HappyNapalm/HAD_CLOCK_191211/firmware/Capt_testboard_code/capt_testboard/usart_transfer_ring_buffer/source/usart_transfer_ring_buffer.c

/*
 * Copyright  2017 NXP
 * All rights reserved.
 *
 *
 * SPDX-License-Identifier: BSD-3-Clause
 */

#include "board.h"
#include "fsl_usart.h"

#include "pin_mux.h"
#include <stdbool.h>
/*******************************************************************************
 * Definitions
 ******************************************************************************/
#define EXAMPLE_USART USART0
#define EXAMPLE_USART_CLK_SRC kCLOCK_MainClk
#define EXAMPLE_USART_CLK_FREQ CLOCK_GetFreq(EXAMPLE_USART_CLK_SRC)
#define DELAY_TIME 0xFFFFFU

#define RX_RING_BUFFER_SIZE 20U
#define ECHO_BUFFER_SIZE 8U

/*******************************************************************************
 * Prototypes
 ******************************************************************************/
static void EXAMPLE_USARTUserCallback(USART_Type *base, usart_handle_t *handle, status_t status, void *userData);
static void EXAMPLE_USARTIinit(void);
static void EXAMPLE_USARTPrepareTransfer(void);

/*******************************************************************************
 * Variables
 ******************************************************************************/
usart_handle_t g_uartHandle;
uint8_t g_tipString[] = "USART RX ring buffer example.\r\nSend back received data.\r\nEcho every 8 bytes.\r\n";
uint8_t g_rxRingBuffer[RX_RING_BUFFER_SIZE] = {0}; /* RX ring buffer. */

uint8_t rxBuffer[ECHO_BUFFER_SIZE] = {0}; /* Buffer for receive data to echo. */
uint8_t txBuffer[ECHO_BUFFER_SIZE] = {0}; /* Buffer for send data to echo. */
volatile bool rxBufferEmpty        = true;
volatile bool txBufferFull         = false;
volatile bool txOnGoing            = false;
volatile bool rxOnGoing            = false;

usart_transfer_t xfer;
usart_transfer_t sendXfer;
usart_transfer_t receiveXfer;

/*******************************************************************************
 * Code
 ******************************************************************************/
/* USART user callback */
void EXAMPLE_USARTUserCallback(USART_Type *base, usart_handle_t *handle, status_t status, void *userData)
{
    userData = userData;

    if (kStatus_USART_TxIdle == status)
    {
        txBufferFull = false;
        txOnGoing    = false;
    }

    if (kStatus_USART_RxIdle == status)
    {
        rxBufferEmpty = false;
        rxOnGoing     = false;
    }
}

/*!
 * @brief Main function
 */
int main(void)
{
    size_t receivedBytes;

    /* Initialize the hardware. */
    /* Initialize the pins. */
    BOARD_InitPins();
    /* Enable clock. */
    BOARD_InitBootClocks();
    /* Select the main clock as source clock of USART0. */
    CLOCK_Select(kUART0_Clk_From_MainClk);

    /* Initialize the USART instance. */
    EXAMPLE_USARTIinit();

    /* Prepare for transactional transmission. */
    EXAMPLE_USARTPrepareTransfer();

    /* Send tip information. */
    txOnGoing = true;
    USART_TransferSendNonBlocking(EXAMPLE_USART, &g_uartHandle, &xfer);

    /* Wait transmit finished. */
    while (txOnGoing)
    {
    }

    while (1)
    {
        /* If txBuffer is empty and rxBuffer is full, copy rxBuffer to txBuffer. */
        if ((!rxBufferEmpty) && (!txBufferFull))
        {
            memcpy(txBuffer, rxBuffer, ECHO_BUFFER_SIZE);
            rxBufferEmpty = true;
            txBufferFull  = true;
        }

        /* If RX is idle and rxBuffer is empty, start to read data to rxBuffer. */
        if ((!rxOnGoing) && rxBufferEmpty)
        {
            rxOnGoing = true;
            USART_TransferReceiveNonBlocking(EXAMPLE_USART, &g_uartHandle, &receiveXfer, &receivedBytes);

            /* The receivedBytes is the current data size when API return, If this value equals to ECHO_BUFFER_SIZE,
             * it means all data were received from ring buffer.
             */
            if (ECHO_BUFFER_SIZE == receivedBytes)
            {
                rxBufferEmpty = false;
                rxOnGoing     = false;
            }
        }

        /* If TX is idle and txBuffer is full, start to send data. */
        if ((!txOnGoing) && txBufferFull)
        {
            txOnGoing = true;
            USART_TransferSendNonBlocking(EXAMPLE_USART, &g_uartHandle, &sendXfer);
        }
    }
}

static void EXAMPLE_USARTIinit(void)
{
    usart_config_t config;

    /* Default config by using USART_GetDefaultConfig():
     * config->baudRate_Bps = 9600U;
     * config->parityMode = kUSART_ParityDisabled;
     * config->stopBitCount = kUSART_OneStopBit;
     * config->bitCountPerChar = kUSART_8BitsPerChar;
     * config->loopback = false;
     * config->enableRx = false;
     * config->enableTx = false;
     * config->syncMode = kUSART_SyncModeDisabled;
     */
    USART_GetDefaultConfig(&config);
    config.baudRate_Bps = BOARD_DEBUG_USART_BAUDRATE;
    config.enableRx     = true;
    config.enableTx     = true;

    /* Initilize the USART with configuration. */
    USART_Init(EXAMPLE_USART, &config, EXAMPLE_USART_CLK_FREQ);
}
static void EXAMPLE_USARTPrepareTransfer(void)
{
    /* Create USART handle and install callback function. */
    USART_TransferCreateHandle(EXAMPLE_USART, &g_uartHandle, EXAMPLE_USARTUserCallback, NULL);
    /* Start ring buffer. */
    USART_TransferStartRingBuffer(EXAMPLE_USART, &g_uartHandle, g_rxRingBuffer, RX_RING_BUFFER_SIZE);

    /* Prepare transfer for sending tip string. */
    xfer.data     = g_tipString;
    xfer.dataSize = sizeof(g_tipString) - 1;

    /* Prepare transfer for sending the received characters. */
    sendXfer.data     = txBuffer;
    sendXfer.dataSize = ECHO_BUFFER_SIZE;

    /* Prepare transfer for receiving characters. */
    receiveXfer.data     = rxBuffer;
    receiveXfer.dataSize = ECHO_BUFFER_SIZE;
}
