HappyNapalm/HAD_CLOCK_191211/firmware/Capt_testboard_code/capt_testboard/gpio_led_output/source/gpio_led_output.c

/*
 * Copyright (c) 2015, Freescale Semiconductor, Inc.
 * Copyright 2016-2018 NXP
 * All rights reserved.
 *
 * SPDX-License-Identifier: BSD-3-Clause
 */

#include "board.h"
#include "fsl_debug_console.h"
#include "fsl_gpio.h"

#include "pin_mux.h"
/*******************************************************************************
 * Definitions
 ******************************************************************************/
#define APP_BOARD_TEST_LED_PORT 0U
#define APP_BOARD_TEST_LED_PIN 11U
#define APP_SW_PORT BOARD_SW1_GPIO_PORT
#define APP_SW_PIN BOARD_SW1_GPIO_PIN


/*******************************************************************************
 * Prototypes
 ******************************************************************************/
/*!
 * @brief delay a while.
 */
void delay(void);

/*******************************************************************************
 * Variables
 ******************************************************************************/

/*******************************************************************************
 * Code
 ******************************************************************************/
void delay(void)
{
    volatile uint32_t i = 0;
    for (i = 0; i < 100000; ++i)
    {
        __asm("NOP"); /* delay */
    }
}

/*!
 * @brief Main function
 */
int main(void)
{
    uint32_t port_state = 0;

    /* Define the init structure for the output LED pin*/
    gpio_pin_config_t led_config = {
        kGPIO_DigitalOutput,
        0,
    };

    /* Board pin, clock, debug console init */
    /* Select the main clock as source clock of USART0 (debug console) */
    CLOCK_Select(BOARD_DEBUG_USART_CLK_ATTACH);

    BOARD_InitPins();
    BOARD_InitBootClocks();
    BOARD_InitDebugConsole();

    /* Print a note to terminal. */
    PRINTF("\r\n GPIO Driver example\r\n");
    PRINTF("\r\n The LED is taking turns to shine.\r\n");

    /* Init output LED GPIO. */
    GPIO_PortInit(GPIO, APP_BOARD_TEST_LED_PORT);
    GPIO_PortInit(GPIO, APP_SW_PORT);
    GPIO_PinInit(GPIO, APP_BOARD_TEST_LED_PORT, APP_BOARD_TEST_LED_PIN, &led_config);
    GPIO_PinWrite(GPIO, APP_BOARD_TEST_LED_PORT, APP_BOARD_TEST_LED_PIN, 1);

    /* Port masking */
    GPIO_PortMaskedSet(GPIO, APP_BOARD_TEST_LED_PORT, 0x0000FFFF);
    GPIO_PortMaskedWrite(GPIO, APP_BOARD_TEST_LED_PORT, 0xFFFFFFFF);
    port_state = GPIO_PortRead(GPIO, APP_BOARD_TEST_LED_PORT);
    PRINTF("\r\n Standard port read: %x\r\n", port_state);
    port_state = GPIO_PortMaskedRead(GPIO, APP_BOARD_TEST_LED_PORT);
    PRINTF("\r\n Masked port read: %x\r\n", port_state);

    while (1)
    {
        port_state = GPIO_PortRead(GPIO, APP_SW_PORT);
        if (!(port_state & (1 << APP_SW_PIN)))
        {
            PRINTF("\r\n Port state: %x\r\n", port_state);
            GPIO_PortToggle(GPIO, APP_BOARD_TEST_LED_PORT, 1u << APP_BOARD_TEST_LED_PIN);
        }
        delay();
    }
}
