HappyNapalm/HAD_CLOCK_191211/firmware/Capt_testboard_code/capt_testboard/capt_acomp/device/LPC804.h

/*
** ###################################################################
**     Processors:          LPC804M101JDH20
**                          LPC804M101JDH24
**                          LPC804M101JHI33
**                          LPC804M111JDH24
**                          LPC804UK
**
**     Compilers:           GNU C Compiler
**                          IAR ANSI C/C++ Compiler for ARM
**                          Keil ARM C/C++ Compiler
**                          MCUXpresso Compiler
**
**     Reference manual:    LPC804 User manual Rev.1.0  24 Jan 2018
**     Version:             rev. 1.0, 2018-01-09
**     Build:               b190306
**
**     Abstract:
**         CMSIS Peripheral Access Layer for LPC804
**
**     Copyright 1997-2016 Freescale Semiconductor, Inc.
**     Copyright 2016-2019 NXP
**     All rights reserved.
**
**     SPDX-License-Identifier: BSD-3-Clause
**
**     http:                 www.nxp.com
**     mail:                 support@nxp.com
**
**     Revisions:
**     - rev. 1.0 (2018-01-09)
**         Initial version.
**
** ###################################################################
*/

/*!
 * @file LPC804.h
 * @version 1.0
 * @date 2018-01-09
 * @brief CMSIS Peripheral Access Layer for LPC804
 *
 * CMSIS Peripheral Access Layer for LPC804
 */

#ifndef _LPC804_H_
#define _LPC804_H_                               /**< Symbol preventing repeated inclusion */

/** Memory map major version (memory maps with equal major version number are
 * compatible) */
#define MCU_MEM_MAP_VERSION 0x0100U
/** Memory map minor version */
#define MCU_MEM_MAP_VERSION_MINOR 0x0000U


/* ----------------------------------------------------------------------------
   -- Interrupt vector numbers
   ---------------------------------------------------------------------------- */

/*!
 * @addtogroup Interrupt_vector_numbers Interrupt vector numbers
 * @{
 */

/** Interrupt Number Definitions */
#define NUMBER_OF_INT_VECTORS 48                 /**< Number of interrupts in the Vector table */

typedef enum IRQn {
  /* Auxiliary constants */
  NotAvail_IRQn                = -128,             /**< Not available device specific interrupt */

  /* Core interrupts */
  NonMaskableInt_IRQn          = -14,              /**< Non Maskable Interrupt */
  HardFault_IRQn               = -13,              /**< Cortex-M0 SV Hard Fault Interrupt */
  SVCall_IRQn                  = -5,               /**< Cortex-M0 SV Call Interrupt */
  PendSV_IRQn                  = -2,               /**< Cortex-M0 Pend SV Interrupt */
  SysTick_IRQn                 = -1,               /**< Cortex-M0 System Tick Interrupt */

  /* Device specific interrupts */
  SPI0_IRQn                    = 0,                /**< SPI0 interrupt */
  Reserved17_IRQn              = 1,                /**< Reserved interrupt */
  DAC0_IRQn                    = 2,                /**< DAC0 interrupt */
  USART0_IRQn                  = 3,                /**< USART0 interrupt */
  USART1_IRQn                  = 4,                /**< USART1 interrupt */
  Reserved21_IRQn              = 5,                /**< Reserved interrupt */
  Reserved22_IRQn              = 6,                /**< Reserved interrupt */
  I2C1_IRQn                    = 7,                /**< I2C1 interrupt */
  I2C0_IRQn                    = 8,                /**< I2C0 interrupt */
  Reserved25_IRQn              = 9,                /**< Reserved interrupt */
  MRT0_IRQn                    = 10,               /**< Multi-rate timer interrupt */
  CMP_CAPT_IRQn                = 11,               /**< Analog comparator interrupt or Capacitive Touch interrupt */
  WDT_IRQn                     = 12,               /**< Windowed watchdog timer interrupt */
  BOD_IRQn                     = 13,               /**< BOD interrupts */
  FLASH_IRQn                   = 14,               /**< flash interrupt */
  WKT_IRQn                     = 15,               /**< Self-wake-up timer interrupt */
  ADC_SEQA_IRQn                = 16,               /**< ADC sequence A completion. */
  ADC_SEQB_IRQn                = 17,               /**< ADC sequence B completion. */
  ADC_THCMP_IRQn               = 18,               /**< ADC threshold compare and error. */
  ADC_OVR_IRQn                 = 19,               /**< ADC overrun */
  Reserved36_IRQn              = 20,               /**< Reserved interrupt */
  Reserved37_IRQn              = 21,               /**< Reserved interrupt */
  Reserved38_IRQn              = 22,               /**< Reserved interrupt */
  CTIMER0_IRQn                 = 23,               /**< Timer interrupt */
  PIN_INT0_IRQn                = 24,               /**< Pin interrupt 0 or pattern match engine slice 0 interrupt */
  PIN_INT1_IRQn                = 25,               /**< Pin interrupt 1 or pattern match engine slice 1 interrupt */
  PIN_INT2_IRQn                = 26,               /**< Pin interrupt 2 or pattern match engine slice 2 interrupt */
  PIN_INT3_IRQn                = 27,               /**< Pin interrupt 3 or pattern match engine slice 3 interrupt */
  PIN_INT4_IRQn                = 28,               /**< Pin interrupt 4 or pattern match engine slice 4 interrupt */
  PIN_INT5_IRQn                = 29,               /**< Pin interrupt 5 or pattern match engine slice 5 interrupt */
  PIN_INT6_IRQn                = 30,               /**< Pin interrupt 6 or pattern match engine slice 6 interrupt */
  PIN_INT7_IRQn                = 31                /**< Pin interrupt 7 or pattern match engine slice 7 interrupt */
} IRQn_Type;

/*!
 * @}
 */ /* end of group Interrupt_vector_numbers */


/* ----------------------------------------------------------------------------
   -- Cortex M0 Core Configuration
   ---------------------------------------------------------------------------- */

/*!
 * @addtogroup Cortex_Core_Configuration Cortex M0 Core Configuration
 * @{
 */

#define __CM0PLUS_REV                  0x0000    /**< Core revision r0p0 */
#define __MPU_PRESENT                  0         /**< Defines if an MPU is present or not */
#define __VTOR_PRESENT                 1         /**< Defines if VTOR is present or not */
#define __NVIC_PRIO_BITS               2         /**< Number of priority bits implemented in the NVIC */
#define __Vendor_SysTickConfig         0         /**< Vendor specific implementation of SysTickConfig is defined */

#include "core_cm0plus.h"              /* Core Peripheral Access Layer */
#include "system_LPC804.h"             /* Device specific configuration file */

/*!
 * @}
 */ /* end of group Cortex_Core_Configuration */


/* ----------------------------------------------------------------------------
   -- Device Peripheral Access Layer
   ---------------------------------------------------------------------------- */

/*!
 * @addtogroup Peripheral_access_layer Device Peripheral Access Layer
 * @{
 */


/*
** Start of section using anonymous unions
*/

#if defined(__ARMCC_VERSION)
  #if (__ARMCC_VERSION >= 6010050)
    #pragma clang diagnostic push
  #else
    #pragma push
    #pragma anon_unions
  #endif
#elif defined(__GNUC__)
  /* anonymous unions are enabled by default */
#elif defined(__IAR_SYSTEMS_ICC__)
  #pragma language=extended
#else
  #error Not supported compiler type
#endif

/* ----------------------------------------------------------------------------
   -- ACOMP Peripheral Access Layer
   ---------------------------------------------------------------------------- */

/*!
 * @addtogroup ACOMP_Peripheral_Access_Layer ACOMP Peripheral Access Layer
 * @{
 */

/** ACOMP - Register Layout Typedef */
typedef struct {
  __IO uint32_t CTRL;                              /**< Comparator control register, offset: 0x0 */
  __IO uint32_t LAD;                               /**< Voltage ladder register, offset: 0x4 */
} ACOMP_Type;

/* ----------------------------------------------------------------------------
   -- ACOMP Register Masks
   ---------------------------------------------------------------------------- */

/*!
 * @addtogroup ACOMP_Register_Masks ACOMP Register Masks
 * @{
 */

/*! @name CTRL - Comparator control register */
/*! @{ */
#define ACOMP_CTRL_EDGESEL_MASK                  (0x18U)
#define ACOMP_CTRL_EDGESEL_SHIFT                 (3U)
/*! EDGESEL - This field controls which edges on the comparator output set the COMPEDGE bit (bit 23 below):
 *  0b00..Falling edges
 *  0b01..Rising edges
 *  0b10..Both edges
 *  0b11..Both edges
 */
#define ACOMP_CTRL_EDGESEL(x)                    (((uint32_t)(((uint32_t)(x)) << ACOMP_CTRL_EDGESEL_SHIFT)) & ACOMP_CTRL_EDGESEL_MASK)
#define ACOMP_CTRL_COMPSA_MASK                   (0x40U)
#define ACOMP_CTRL_COMPSA_SHIFT                  (6U)
/*! COMPSA - Comparator output control
 *  0b0..Comparator output is used directly.
 *  0b1..Comparator output is synchronized to the bus clock for output to other modules.
 */
#define ACOMP_CTRL_COMPSA(x)                     (((uint32_t)(((uint32_t)(x)) << ACOMP_CTRL_COMPSA_SHIFT)) & ACOMP_CTRL_COMPSA_MASK)
#define ACOMP_CTRL_COMP_VP_SEL_MASK              (0x700U)
#define ACOMP_CTRL_COMP_VP_SEL_SHIFT             (8U)
/*! COMP_VP_SEL - Selects positive voltage input
 *  0b000..VOLTAGE_LADDER_OUTPUT
 *  0b001..ACMP_I1
 *  0b010..ACMP_I2
 *  0b011..ACMP_I3
 *  0b100..ACMP_I4
 *  0b101..ACMP_I5
 *  0b110..Band gap. Internal reference voltage.
 *  0b111..DAC0 output
 */
#define ACOMP_CTRL_COMP_VP_SEL(x)                (((uint32_t)(((uint32_t)(x)) << ACOMP_CTRL_COMP_VP_SEL_SHIFT)) & ACOMP_CTRL_COMP_VP_SEL_MASK)
#define ACOMP_CTRL_COMP_VM_SEL_MASK              (0x3800U)
#define ACOMP_CTRL_COMP_VM_SEL_SHIFT             (11U)
/*! COMP_VM_SEL - Selects negative voltage input
 *  0b000..VOLTAGE_LADDER_OUTPUT
 *  0b001..ACMP_I1
 *  0b010..ACMP_I2
 *  0b011..ACMP_I3
 *  0b100..ACMP_I4
 *  0b101..ACMP_I5
 *  0b110..Band gap. Internal reference voltage.
 *  0b111..DAC0 output
 */
#define ACOMP_CTRL_COMP_VM_SEL(x)                (((uint32_t)(((uint32_t)(x)) << ACOMP_CTRL_COMP_VM_SEL_SHIFT)) & ACOMP_CTRL_COMP_VM_SEL_MASK)
#define ACOMP_CTRL_EDGECLR_MASK                  (0x100000U)
#define ACOMP_CTRL_EDGECLR_SHIFT                 (20U)
#define ACOMP_CTRL_EDGECLR(x)                    (((uint32_t)(((uint32_t)(x)) << ACOMP_CTRL_EDGECLR_SHIFT)) & ACOMP_CTRL_EDGECLR_MASK)
#define ACOMP_CTRL_COMPSTAT_MASK                 (0x200000U)
#define ACOMP_CTRL_COMPSTAT_SHIFT                (21U)
#define ACOMP_CTRL_COMPSTAT(x)                   (((uint32_t)(((uint32_t)(x)) << ACOMP_CTRL_COMPSTAT_SHIFT)) & ACOMP_CTRL_COMPSTAT_MASK)
#define ACOMP_CTRL_COMPEDGE_MASK                 (0x800000U)
#define ACOMP_CTRL_COMPEDGE_SHIFT                (23U)
#define ACOMP_CTRL_COMPEDGE(x)                   (((uint32_t)(((uint32_t)(x)) << ACOMP_CTRL_COMPEDGE_SHIFT)) & ACOMP_CTRL_COMPEDGE_MASK)
#define ACOMP_CTRL_INTENA_MASK                   (0x1000000U)
#define ACOMP_CTRL_INTENA_SHIFT                  (24U)
#define ACOMP_CTRL_INTENA(x)                     (((uint32_t)(((uint32_t)(x)) << ACOMP_CTRL_INTENA_SHIFT)) & ACOMP_CTRL_INTENA_MASK)
#define ACOMP_CTRL_HYS_MASK                      (0x6000000U)
#define ACOMP_CTRL_HYS_SHIFT                     (25U)
/*! HYS - Controls the hysteresis of the comparator. When the comparator is outputting a certain
 *    state, this is the difference between the selected signals, in the opposite direction from the
 *    state being output, that will switch the output.
 *  0b00..None (the output will switch as the voltages cross)
 *  0b01..5 mv
 *  0b10..10 mv
 *  0b11..20 mv
 */
#define ACOMP_CTRL_HYS(x)                        (((uint32_t)(((uint32_t)(x)) << ACOMP_CTRL_HYS_SHIFT)) & ACOMP_CTRL_HYS_MASK)
/*! @} */

/*! @name LAD - Voltage ladder register */
/*! @{ */
#define ACOMP_LAD_LADEN_MASK                     (0x1U)
#define ACOMP_LAD_LADEN_SHIFT                    (0U)
#define ACOMP_LAD_LADEN(x)                       (((uint32_t)(((uint32_t)(x)) << ACOMP_LAD_LADEN_SHIFT)) & ACOMP_LAD_LADEN_MASK)
#define ACOMP_LAD_LADSEL_MASK                    (0x3EU)
#define ACOMP_LAD_LADSEL_SHIFT                   (1U)
#define ACOMP_LAD_LADSEL(x)                      (((uint32_t)(((uint32_t)(x)) << ACOMP_LAD_LADSEL_SHIFT)) & ACOMP_LAD_LADSEL_MASK)
#define ACOMP_LAD_LADREF_MASK                    (0x40U)
#define ACOMP_LAD_LADREF_SHIFT                   (6U)
/*! LADREF - Selects the reference voltage Vref for the voltage ladder.
 *  0b0..Supply pin VDD
 *  0b1..VDDCMP pin
 */
#define ACOMP_LAD_LADREF(x)                      (((uint32_t)(((uint32_t)(x)) << ACOMP_LAD_LADREF_SHIFT)) & ACOMP_LAD_LADREF_MASK)
/*! @} */


/*!
 * @}
 */ /* end of group ACOMP_Register_Masks */


/* ACOMP - Peripheral instance base addresses */
/** Peripheral ACOMP base address */
#define ACOMP_BASE                               (0x40024000u)
/** Peripheral ACOMP base pointer */
#define ACOMP                                    ((ACOMP_Type *)ACOMP_BASE)
/** Array initializer of ACOMP peripheral base addresses */
#define ACOMP_BASE_ADDRS                         { ACOMP_BASE }
/** Array initializer of ACOMP peripheral base pointers */
#define ACOMP_BASE_PTRS                          { ACOMP }

/*!
 * @}
 */ /* end of group ACOMP_Peripheral_Access_Layer */


/* ----------------------------------------------------------------------------
   -- ADC Peripheral Access Layer
   ---------------------------------------------------------------------------- */

/*!
 * @addtogroup ADC_Peripheral_Access_Layer ADC Peripheral Access Layer
 * @{
 */

/** ADC - Register Layout Typedef */
typedef struct {
  __IO uint32_t CTRL;                              /**< ADC Control register. Contains the clock divide value, resolution selection, sampling time selection, and mode controls., offset: 0x0 */
       uint8_t RESERVED_0[4];
  __IO uint32_t SEQ_CTRL[2];                       /**< ADC Conversion Sequence-n control register: Controls triggering and channel selection for conversion sequence-n. Also specifies interrupt mode for sequence-n., array offset: 0x8, array step: 0x4 */
  __I  uint32_t SEQ_GDAT[2];                       /**< ADC Sequence-n Global Data register. This register contains the result of the most recent ADC conversion performed under sequence-n., array offset: 0x10, array step: 0x4 */
       uint8_t RESERVED_1[8];
  __I  uint32_t DAT[12];                           /**< ADC Channel N Data register. This register contains the result of the most recent conversion completed on channel N., array offset: 0x20, array step: 0x4 */
  __IO uint32_t THR0_LOW;                          /**< ADC Low Compare Threshold register 0: Contains the lower threshold level for automatic threshold comparison for any channels linked to threshold pair 0., offset: 0x50 */
  __IO uint32_t THR1_LOW;                          /**< ADC Low Compare Threshold register 1: Contains the lower threshold level for automatic threshold comparison for any channels linked to threshold pair 1., offset: 0x54 */
  __IO uint32_t THR0_HIGH;                         /**< ADC High Compare Threshold register 0: Contains the upper threshold level for automatic threshold comparison for any channels linked to threshold pair 0., offset: 0x58 */
  __IO uint32_t THR1_HIGH;                         /**< ADC High Compare Threshold register 1: Contains the upper threshold level for automatic threshold comparison for any channels linked to threshold pair 1., offset: 0x5C */
  __IO uint32_t CHAN_THRSEL;                       /**< ADC Channel-Threshold Select register. Specifies which set of threshold compare registers are to be used for each channel, offset: 0x60 */
  __IO uint32_t INTEN;                             /**< ADC Interrupt Enable register. This register contains enable bits that enable the sequence-A, sequence-B, threshold compare and data overrun interrupts to be generated., offset: 0x64 */
  __IO uint32_t FLAGS;                             /**< ADC Flags register. Contains the four interrupt/DMA trigger flags and the individual component overrun and threshold-compare flags. (The overrun bits replicate information stored in the result registers)., offset: 0x68 */
} ADC_Type;

/* ----------------------------------------------------------------------------
   -- ADC Register Masks
   ---------------------------------------------------------------------------- */

/*!
 * @addtogroup ADC_Register_Masks ADC Register Masks
 * @{
 */

/*! @name CTRL - ADC Control register. Contains the clock divide value, resolution selection, sampling time selection, and mode controls. */
/*! @{ */
#define ADC_CTRL_CLKDIV_MASK                     (0xFFU)
#define ADC_CTRL_CLKDIV_SHIFT                    (0U)
#define ADC_CTRL_CLKDIV(x)                       (((uint32_t)(((uint32_t)(x)) << ADC_CTRL_CLKDIV_SHIFT)) & ADC_CTRL_CLKDIV_MASK)
#define ADC_CTRL_LPWRMODE_MASK                   (0x400U)
#define ADC_CTRL_LPWRMODE_SHIFT                  (10U)
/*! LPWRMODE - The low-power ADC mode
 *  0b0..The low-power ADC mode is disabled. The analog circuitry remains activated even when no conversions are requested.
 *  0b1..The low-power ADC mode is enabled. The analog circuitry is automatically powered-down when no conversions
 *       are taking place. When any (hardware or software) triggering event is detected, the analog circuitry is
 *       enabled. After the required start-up time, the requested conversion will be launched. Once the conversion
 *       completes, the analog-circuitry will again be powered-down provided no further conversions are pending.
 *       Using this mode can save an appreciable amount of current (approximately 2.5 mA) when conversions are
 *       required relatively infrequently. The penalty for using this mode is an approximately FIFTEEN ADC CLOCK delay (30
 *       clocks in 10-bit mode), based on the frequency specified in the CLKDIV field, from the time the trigger
 *       event occurs until sampling of the A/D input commences. Note: This mode will NOT power-up the A/D if the
 *       ADC_ENA bit is low.
 */
#define ADC_CTRL_LPWRMODE(x)                     (((uint32_t)(((uint32_t)(x)) << ADC_CTRL_LPWRMODE_SHIFT)) & ADC_CTRL_LPWRMODE_MASK)
/*! @} */

/*! @name SEQ_CTRL - ADC Conversion Sequence-n control register: Controls triggering and channel selection for conversion sequence-n. Also specifies interrupt mode for sequence-n. */
/*! @{ */
#define ADC_SEQ_CTRL_CHANNELS_MASK               (0xFFFU)
#define ADC_SEQ_CTRL_CHANNELS_SHIFT              (0U)
#define ADC_SEQ_CTRL_CHANNELS(x)                 (((uint32_t)(((uint32_t)(x)) << ADC_SEQ_CTRL_CHANNELS_SHIFT)) & ADC_SEQ_CTRL_CHANNELS_MASK)
#define ADC_SEQ_CTRL_TRIGGER_MASK                (0x7000U)
#define ADC_SEQ_CTRL_TRIGGER_SHIFT               (12U)
#define ADC_SEQ_CTRL_TRIGGER(x)                  (((uint32_t)(((uint32_t)(x)) << ADC_SEQ_CTRL_TRIGGER_SHIFT)) & ADC_SEQ_CTRL_TRIGGER_MASK)
#define ADC_SEQ_CTRL_TRIGPOL_MASK                (0x40000U)
#define ADC_SEQ_CTRL_TRIGPOL_SHIFT               (18U)
/*! TRIGPOL - Select the polarity of the selected input trigger for this conversion sequence. In
 *    order to avoid generating a spurious trigger, it is recommended writing to this field only when
 *    SEQA_ENA (bit 31) is low. It is safe to change this field and set bit 31 in the same write.
 *  0b0..Negative edge. A negative edge launches the conversion sequence on the selected trigger input.
 *  0b1..Positive edge. A positive edge launches the conversion sequence on the selected trigger input.
 */
#define ADC_SEQ_CTRL_TRIGPOL(x)                  (((uint32_t)(((uint32_t)(x)) << ADC_SEQ_CTRL_TRIGPOL_SHIFT)) & ADC_SEQ_CTRL_TRIGPOL_MASK)
#define ADC_SEQ_CTRL_SYNCBYPASS_MASK             (0x80000U)
#define ADC_SEQ_CTRL_SYNCBYPASS_SHIFT            (19U)
/*! SYNCBYPASS - Setting this bit allows the hardware trigger input to bypass synchronization
 *    flip-flop stages and therefore shorten the time between the trigger input signal and the start of a
 *    conversion. There are slightly different criteria for whether or not this bit can be set
 *    depending on the clock operating mode: Synchronous mode (the ASYNMODE in the CTRL register = 0):
 *    Synchronization may be bypassed (this bit may be set) if the selected trigger source is already
 *    synchronous with the main system clock (eg. coming from an on-chip, system-clock-based timer).
 *    Whether this bit is set or not, a trigger pulse must be maintained for at least one system
 *    clock period. Asynchronous mode (the ASYNMODE in the CTRL register = 1): Synchronization may be
 *    bypassed (this bit may be set) if it is certain that the duration of a trigger input pulse
 *    will be at least one cycle of the ADC clock (regardless of whether the trigger comes from and
 *    on-chip or off-chip source). If this bit is NOT set, the trigger pulse must at least be
 *    maintained for one system clock period.
 *  0b0..Enable trigger synchronization. The hardware trigger bypass is not enabled.
 *  0b1..Bypass trigger synchronization. The hardware trigger bypass is enabled.
 */
#define ADC_SEQ_CTRL_SYNCBYPASS(x)               (((uint32_t)(((uint32_t)(x)) << ADC_SEQ_CTRL_SYNCBYPASS_SHIFT)) & ADC_SEQ_CTRL_SYNCBYPASS_MASK)
#define ADC_SEQ_CTRL_TSAMP_MASK                  (0x1F00000U)
#define ADC_SEQ_CTRL_TSAMP_SHIFT                 (20U)
#define ADC_SEQ_CTRL_TSAMP(x)                    (((uint32_t)(((uint32_t)(x)) << ADC_SEQ_CTRL_TSAMP_SHIFT)) & ADC_SEQ_CTRL_TSAMP_MASK)
#define ADC_SEQ_CTRL_START_MASK                  (0x4000000U)
#define ADC_SEQ_CTRL_START_SHIFT                 (26U)
#define ADC_SEQ_CTRL_START(x)                    (((uint32_t)(((uint32_t)(x)) << ADC_SEQ_CTRL_START_SHIFT)) & ADC_SEQ_CTRL_START_MASK)
#define ADC_SEQ_CTRL_BURST_MASK                  (0x8000000U)
#define ADC_SEQ_CTRL_BURST_SHIFT                 (27U)
#define ADC_SEQ_CTRL_BURST(x)                    (((uint32_t)(((uint32_t)(x)) << ADC_SEQ_CTRL_BURST_SHIFT)) & ADC_SEQ_CTRL_BURST_MASK)
#define ADC_SEQ_CTRL_SINGLESTEP_MASK             (0x10000000U)
#define ADC_SEQ_CTRL_SINGLESTEP_SHIFT            (28U)
#define ADC_SEQ_CTRL_SINGLESTEP(x)               (((uint32_t)(((uint32_t)(x)) << ADC_SEQ_CTRL_SINGLESTEP_SHIFT)) & ADC_SEQ_CTRL_SINGLESTEP_MASK)
#define ADC_SEQ_CTRL_LOWPRIO_MASK                (0x20000000U)
#define ADC_SEQ_CTRL_LOWPRIO_SHIFT               (29U)
/*! LOWPRIO - Set priority for sequence A.
 *  0b0..Low priority. Any B trigger which occurs while an A conversion sequence is active will be ignored and lost.
 *  0b1..High priority. Setting this bit to a 1 will permit any enabled B sequence trigger (including a B sequence
 *       software start) to immediately interrupt sequence A and launch a B sequence in it's place. The conversion
 *       currently in progress will be terminated. The A sequence that was interrupted will automatically resume
 *       after the B sequence completes. The channel whose conversion was terminated will be re-sampled and the
 *       conversion sequence will resume from that point.
 */
#define ADC_SEQ_CTRL_LOWPRIO(x)                  (((uint32_t)(((uint32_t)(x)) << ADC_SEQ_CTRL_LOWPRIO_SHIFT)) & ADC_SEQ_CTRL_LOWPRIO_MASK)
#define ADC_SEQ_CTRL_MODE_MASK                   (0x40000000U)
#define ADC_SEQ_CTRL_MODE_SHIFT                  (30U)
/*! MODE - Indicates whether the primary method for retrieving conversion results for this sequence
 *    will be accomplished via reading the global data register (SEQA_GDAT) at the end of each
 *    conversion, or the individual channel result registers at the end of the entire sequence. Impacts
 *    when conversion-complete interrupt/DMA trigger for sequence-A will be generated and which
 *    overrun conditions contribute to an overrun interrupt as described below.
 *  0b0..End of conversion. The sequence A interrupt/DMA trigger will be set at the end of each individual ADC
 *       conversion performed under sequence A. This flag will mirror the DATAVALID bit in the SEQA_GDAT register. The
 *       OVERRUN bit in the SEQA_GDAT register will contribute to generation of an overrun interrupt/DMA trigger
 *       if enabled.
 *  0b1..End of sequence. The sequence A interrupt/DMA trigger will be set when the entire set of sequence-A
 *       conversions completes. This flag will need to be explicitly cleared by software or by the DMA-clear signal in
 *       this mode. The OVERRUN bit in the SEQA_GDAT register will NOT contribute to generation of an overrun
 *       interrupt/DMA trigger since it is assumed this register may not be utilized in this mode.
 */
#define ADC_SEQ_CTRL_MODE(x)                     (((uint32_t)(((uint32_t)(x)) << ADC_SEQ_CTRL_MODE_SHIFT)) & ADC_SEQ_CTRL_MODE_MASK)
#define ADC_SEQ_CTRL_SEQ_ENA_MASK                (0x80000000U)
#define ADC_SEQ_CTRL_SEQ_ENA_SHIFT               (31U)
/*! SEQ_ENA - Sequence Enable. In order to avoid spuriously triggering the sequence, care should be
 *    taken to only set the SEQn_ENA bit when the selected trigger input is in its INACTIVE state
 *    (as defined by the TRIGPOL bit). If this condition is not met, the sequence will be triggered
 *    immediately upon being enabled. In order to avoid spuriously triggering the sequence, care
 *    should be taken to only set the SEQn_ENA bit when the selected trigger input is in its INACTIVE
 *    state (as defined by the TRIGPOL bit). If this condition is not met, the sequence will be
 *    triggered immediately upon being enabled.
 *  0b0..Disabled. Sequence n is disabled. Sequence n triggers are ignored. If this bit is cleared while sequence
 *       n is in progress, the sequence will be halted at the end of the current conversion. After the sequence is
 *       re-enabled, a new trigger will be required to restart the sequence beginning with the next enabled channel.
 *  0b1..Enabled. Sequence n is enabled.
 */
#define ADC_SEQ_CTRL_SEQ_ENA(x)                  (((uint32_t)(((uint32_t)(x)) << ADC_SEQ_CTRL_SEQ_ENA_SHIFT)) & ADC_SEQ_CTRL_SEQ_ENA_MASK)
/*! @} */

/* The count of ADC_SEQ_CTRL */
#define ADC_SEQ_CTRL_COUNT                       (2U)

/*! @name SEQ_GDAT - ADC Sequence-n Global Data register. This register contains the result of the most recent ADC conversion performed under sequence-n. */
/*! @{ */
#define ADC_SEQ_GDAT_RESULT_MASK                 (0xFFF0U)
#define ADC_SEQ_GDAT_RESULT_SHIFT                (4U)
#define ADC_SEQ_GDAT_RESULT(x)                   (((uint32_t)(((uint32_t)(x)) << ADC_SEQ_GDAT_RESULT_SHIFT)) & ADC_SEQ_GDAT_RESULT_MASK)
#define ADC_SEQ_GDAT_THCMPRANGE_MASK             (0x30000U)
#define ADC_SEQ_GDAT_THCMPRANGE_SHIFT            (16U)
#define ADC_SEQ_GDAT_THCMPRANGE(x)               (((uint32_t)(((uint32_t)(x)) << ADC_SEQ_GDAT_THCMPRANGE_SHIFT)) & ADC_SEQ_GDAT_THCMPRANGE_MASK)
#define ADC_SEQ_GDAT_THCMPCROSS_MASK             (0xC0000U)
#define ADC_SEQ_GDAT_THCMPCROSS_SHIFT            (18U)
#define ADC_SEQ_GDAT_THCMPCROSS(x)               (((uint32_t)(((uint32_t)(x)) << ADC_SEQ_GDAT_THCMPCROSS_SHIFT)) & ADC_SEQ_GDAT_THCMPCROSS_MASK)
#define ADC_SEQ_GDAT_CHN_MASK                    (0x3C000000U)
#define ADC_SEQ_GDAT_CHN_SHIFT                   (26U)
#define ADC_SEQ_GDAT_CHN(x)                      (((uint32_t)(((uint32_t)(x)) << ADC_SEQ_GDAT_CHN_SHIFT)) & ADC_SEQ_GDAT_CHN_MASK)
#define ADC_SEQ_GDAT_OVERRUN_MASK                (0x40000000U)
#define ADC_SEQ_GDAT_OVERRUN_SHIFT               (30U)
#define ADC_SEQ_GDAT_OVERRUN(x)                  (((uint32_t)(((uint32_t)(x)) << ADC_SEQ_GDAT_OVERRUN_SHIFT)) & ADC_SEQ_GDAT_OVERRUN_MASK)
#define ADC_SEQ_GDAT_DATAVALID_MASK              (0x80000000U)
#define ADC_SEQ_GDAT_DATAVALID_SHIFT             (31U)
#define ADC_SEQ_GDAT_DATAVALID(x)                (((uint32_t)(((uint32_t)(x)) << ADC_SEQ_GDAT_DATAVALID_SHIFT)) & ADC_SEQ_GDAT_DATAVALID_MASK)
/*! @} */

/* The count of ADC_SEQ_GDAT */
#define ADC_SEQ_GDAT_COUNT                       (2U)

/*! @name DAT - ADC Channel N Data register. This register contains the result of the most recent conversion completed on channel N. */
/*! @{ */
#define ADC_DAT_RESULT_MASK                      (0xFFF0U)
#define ADC_DAT_RESULT_SHIFT                     (4U)
#define ADC_DAT_RESULT(x)                        (((uint32_t)(((uint32_t)(x)) << ADC_DAT_RESULT_SHIFT)) & ADC_DAT_RESULT_MASK)
#define ADC_DAT_THCMPRANGE_MASK                  (0x30000U)
#define ADC_DAT_THCMPRANGE_SHIFT                 (16U)
#define ADC_DAT_THCMPRANGE(x)                    (((uint32_t)(((uint32_t)(x)) << ADC_DAT_THCMPRANGE_SHIFT)) & ADC_DAT_THCMPRANGE_MASK)
#define ADC_DAT_THCMPCROSS_MASK                  (0xC0000U)
#define ADC_DAT_THCMPCROSS_SHIFT                 (18U)
#define ADC_DAT_THCMPCROSS(x)                    (((uint32_t)(((uint32_t)(x)) << ADC_DAT_THCMPCROSS_SHIFT)) & ADC_DAT_THCMPCROSS_MASK)
#define ADC_DAT_CHANNEL_MASK                     (0x3C000000U)
#define ADC_DAT_CHANNEL_SHIFT                    (26U)
#define ADC_DAT_CHANNEL(x)                       (((uint32_t)(((uint32_t)(x)) << ADC_DAT_CHANNEL_SHIFT)) & ADC_DAT_CHANNEL_MASK)
#define ADC_DAT_OVERRUN_MASK                     (0x40000000U)
#define ADC_DAT_OVERRUN_SHIFT                    (30U)
#define ADC_DAT_OVERRUN(x)                       (((uint32_t)(((uint32_t)(x)) << ADC_DAT_OVERRUN_SHIFT)) & ADC_DAT_OVERRUN_MASK)
#define ADC_DAT_DATAVALID_MASK                   (0x80000000U)
#define ADC_DAT_DATAVALID_SHIFT                  (31U)
#define ADC_DAT_DATAVALID(x)                     (((uint32_t)(((uint32_t)(x)) << ADC_DAT_DATAVALID_SHIFT)) & ADC_DAT_DATAVALID_MASK)
/*! @} */

/* The count of ADC_DAT */
#define ADC_DAT_COUNT                            (12U)

/*! @name THR0_LOW - ADC Low Compare Threshold register 0: Contains the lower threshold level for automatic threshold comparison for any channels linked to threshold pair 0. */
/*! @{ */
#define ADC_THR0_LOW_THRLOW_MASK                 (0xFFF0U)
#define ADC_THR0_LOW_THRLOW_SHIFT                (4U)
#define ADC_THR0_LOW_THRLOW(x)                   (((uint32_t)(((uint32_t)(x)) << ADC_THR0_LOW_THRLOW_SHIFT)) & ADC_THR0_LOW_THRLOW_MASK)
/*! @} */

/*! @name THR1_LOW - ADC Low Compare Threshold register 1: Contains the lower threshold level for automatic threshold comparison for any channels linked to threshold pair 1. */
/*! @{ */
#define ADC_THR1_LOW_THRLOW_MASK                 (0xFFF0U)
#define ADC_THR1_LOW_THRLOW_SHIFT                (4U)
#define ADC_THR1_LOW_THRLOW(x)                   (((uint32_t)(((uint32_t)(x)) << ADC_THR1_LOW_THRLOW_SHIFT)) & ADC_THR1_LOW_THRLOW_MASK)
/*! @} */

/*! @name THR0_HIGH - ADC High Compare Threshold register 0: Contains the upper threshold level for automatic threshold comparison for any channels linked to threshold pair 0. */
/*! @{ */
#define ADC_THR0_HIGH_THRHIGH_MASK               (0xFFF0U)
#define ADC_THR0_HIGH_THRHIGH_SHIFT              (4U)
#define ADC_THR0_HIGH_THRHIGH(x)                 (((uint32_t)(((uint32_t)(x)) << ADC_THR0_HIGH_THRHIGH_SHIFT)) & ADC_THR0_HIGH_THRHIGH_MASK)
/*! @} */

/*! @name THR1_HIGH - ADC High Compare Threshold register 1: Contains the upper threshold level for automatic threshold comparison for any channels linked to threshold pair 1. */
/*! @{ */
#define ADC_THR1_HIGH_THRHIGH_MASK               (0xFFF0U)
#define ADC_THR1_HIGH_THRHIGH_SHIFT              (4U)
#define ADC_THR1_HIGH_THRHIGH(x)                 (((uint32_t)(((uint32_t)(x)) << ADC_THR1_HIGH_THRHIGH_SHIFT)) & ADC_THR1_HIGH_THRHIGH_MASK)
/*! @} */

/*! @name CHAN_THRSEL - ADC Channel-Threshold Select register. Specifies which set of threshold compare registers are to be used for each channel */
/*! @{ */
#define ADC_CHAN_THRSEL_CH0_THRSEL_MASK          (0x1U)
#define ADC_CHAN_THRSEL_CH0_THRSEL_SHIFT         (0U)
/*! CH0_THRSEL - Threshold select for channel 0.
 *  0b0..Threshold 0. Results for this channel will be compared against the threshold levels indicated in the THR0_LOW and THR0_HIGH registers.
 *  0b1..Threshold 1. Results for this channel will be compared against the threshold levels indicated in the THR1_LOW and THR1_HIGH registers.
 */
#define ADC_CHAN_THRSEL_CH0_THRSEL(x)            (((uint32_t)(((uint32_t)(x)) << ADC_CHAN_THRSEL_CH0_THRSEL_SHIFT)) & ADC_CHAN_THRSEL_CH0_THRSEL_MASK)
#define ADC_CHAN_THRSEL_CH1_THRSEL_MASK          (0x2U)
#define ADC_CHAN_THRSEL_CH1_THRSEL_SHIFT         (1U)
#define ADC_CHAN_THRSEL_CH1_THRSEL(x)            (((uint32_t)(((uint32_t)(x)) << ADC_CHAN_THRSEL_CH1_THRSEL_SHIFT)) & ADC_CHAN_THRSEL_CH1_THRSEL_MASK)
#define ADC_CHAN_THRSEL_CH2_THRSEL_MASK          (0x4U)
#define ADC_CHAN_THRSEL_CH2_THRSEL_SHIFT         (2U)
#define ADC_CHAN_THRSEL_CH2_THRSEL(x)            (((uint32_t)(((uint32_t)(x)) << ADC_CHAN_THRSEL_CH2_THRSEL_SHIFT)) & ADC_CHAN_THRSEL_CH2_THRSEL_MASK)
#define ADC_CHAN_THRSEL_CH3_THRSEL_MASK          (0x8U)
#define ADC_CHAN_THRSEL_CH3_THRSEL_SHIFT         (3U)
#define ADC_CHAN_THRSEL_CH3_THRSEL(x)            (((uint32_t)(((uint32_t)(x)) << ADC_CHAN_THRSEL_CH3_THRSEL_SHIFT)) & ADC_CHAN_THRSEL_CH3_THRSEL_MASK)
#define ADC_CHAN_THRSEL_CH4_THRSEL_MASK          (0x10U)
#define ADC_CHAN_THRSEL_CH4_THRSEL_SHIFT         (4U)
#define ADC_CHAN_THRSEL_CH4_THRSEL(x)            (((uint32_t)(((uint32_t)(x)) << ADC_CHAN_THRSEL_CH4_THRSEL_SHIFT)) & ADC_CHAN_THRSEL_CH4_THRSEL_MASK)
#define ADC_CHAN_THRSEL_CH5_THRSEL_MASK          (0x20U)
#define ADC_CHAN_THRSEL_CH5_THRSEL_SHIFT         (5U)
#define ADC_CHAN_THRSEL_CH5_THRSEL(x)            (((uint32_t)(((uint32_t)(x)) << ADC_CHAN_THRSEL_CH5_THRSEL_SHIFT)) & ADC_CHAN_THRSEL_CH5_THRSEL_MASK)
#define ADC_CHAN_THRSEL_CH6_THRSEL_MASK          (0x40U)
#define ADC_CHAN_THRSEL_CH6_THRSEL_SHIFT         (6U)
#define ADC_CHAN_THRSEL_CH6_THRSEL(x)            (((uint32_t)(((uint32_t)(x)) << ADC_CHAN_THRSEL_CH6_THRSEL_SHIFT)) & ADC_CHAN_THRSEL_CH6_THRSEL_MASK)
#define ADC_CHAN_THRSEL_CH7_THRSEL_MASK          (0x80U)
#define ADC_CHAN_THRSEL_CH7_THRSEL_SHIFT         (7U)
#define ADC_CHAN_THRSEL_CH7_THRSEL(x)            (((uint32_t)(((uint32_t)(x)) << ADC_CHAN_THRSEL_CH7_THRSEL_SHIFT)) & ADC_CHAN_THRSEL_CH7_THRSEL_MASK)
#define ADC_CHAN_THRSEL_CH8_THRSEL_MASK          (0x100U)
#define ADC_CHAN_THRSEL_CH8_THRSEL_SHIFT         (8U)
#define ADC_CHAN_THRSEL_CH8_THRSEL(x)            (((uint32_t)(((uint32_t)(x)) << ADC_CHAN_THRSEL_CH8_THRSEL_SHIFT)) & ADC_CHAN_THRSEL_CH8_THRSEL_MASK)
#define ADC_CHAN_THRSEL_CH9_THRSEL_MASK          (0x200U)
#define ADC_CHAN_THRSEL_CH9_THRSEL_SHIFT         (9U)
#define ADC_CHAN_THRSEL_CH9_THRSEL(x)            (((uint32_t)(((uint32_t)(x)) << ADC_CHAN_THRSEL_CH9_THRSEL_SHIFT)) & ADC_CHAN_THRSEL_CH9_THRSEL_MASK)
#define ADC_CHAN_THRSEL_CH10_THRSEL_MASK         (0x400U)
#define ADC_CHAN_THRSEL_CH10_THRSEL_SHIFT        (10U)
#define ADC_CHAN_THRSEL_CH10_THRSEL(x)           (((uint32_t)(((uint32_t)(x)) << ADC_CHAN_THRSEL_CH10_THRSEL_SHIFT)) & ADC_CHAN_THRSEL_CH10_THRSEL_MASK)
#define ADC_CHAN_THRSEL_CH11_THRSEL_MASK         (0x800U)
#define ADC_CHAN_THRSEL_CH11_THRSEL_SHIFT        (11U)
#define ADC_CHAN_THRSEL_CH11_THRSEL(x)           (((uint32_t)(((uint32_t)(x)) << ADC_CHAN_THRSEL_CH11_THRSEL_SHIFT)) & ADC_CHAN_THRSEL_CH11_THRSEL_MASK)
/*! @} */

/*! @name INTEN - ADC Interrupt Enable register. This register contains enable bits that enable the sequence-A, sequence-B, threshold compare and data overrun interrupts to be generated. */
/*! @{ */
#define ADC_INTEN_SEQA_INTEN_MASK                (0x1U)
#define ADC_INTEN_SEQA_INTEN_SHIFT               (0U)
/*! SEQA_INTEN - Sequence A interrupt enable.
 *  0b0..Disabled. The sequence A interrupt/DMA trigger is disabled.
 *  0b1..Enabled. The sequence A interrupt/DMA trigger is enabled and will be asserted either upon completion of
 *       each individual conversion performed as part of sequence A, or upon completion of the entire A sequence of
 *       conversions, depending on the MODE bit in the SEQA_CTRL register.
 */
#define ADC_INTEN_SEQA_INTEN(x)                  (((uint32_t)(((uint32_t)(x)) << ADC_INTEN_SEQA_INTEN_SHIFT)) & ADC_INTEN_SEQA_INTEN_MASK)
#define ADC_INTEN_SEQB_INTEN_MASK                (0x2U)
#define ADC_INTEN_SEQB_INTEN_SHIFT               (1U)
/*! SEQB_INTEN - Sequence B interrupt enable.
 *  0b0..Disabled. The sequence B interrupt/DMA trigger is disabled.
 *  0b1..Enabled. The sequence B interrupt/DMA trigger is enabled and will be asserted either upon completion of
 *       each individual conversion performed as part of sequence B, or upon completion of the entire B sequence of
 *       conversions, depending on the MODE bit in the SEQB_CTRL register.
 */
#define ADC_INTEN_SEQB_INTEN(x)                  (((uint32_t)(((uint32_t)(x)) << ADC_INTEN_SEQB_INTEN_SHIFT)) & ADC_INTEN_SEQB_INTEN_MASK)
#define ADC_INTEN_OVR_INTEN_MASK                 (0x4U)
#define ADC_INTEN_OVR_INTEN_SHIFT                (2U)
/*! OVR_INTEN - Overrun interrupt enable.
 *  0b0..Disabled. The overrun interrupt is disabled.
 *  0b1..Enabled. The overrun interrupt is enabled. Detection of an overrun condition on any of the 12 channel
 *       data registers will cause an overrun interrupt/DMA trigger. In addition, if the MODE bit for a particular
 *       sequence is 0, then an overrun in the global data register for that sequence will also cause this
 *       interrupt/DMA trigger to be asserted.
 */
#define ADC_INTEN_OVR_INTEN(x)                   (((uint32_t)(((uint32_t)(x)) << ADC_INTEN_OVR_INTEN_SHIFT)) & ADC_INTEN_OVR_INTEN_MASK)
#define ADC_INTEN_ADCMPINTEN0_MASK               (0x18U)
#define ADC_INTEN_ADCMPINTEN0_SHIFT              (3U)
/*! ADCMPINTEN0 - Threshold comparison interrupt enable for channel 0.
 *  0b00..Disabled.
 *  0b01..Outside threshold.
 *  0b10..Crossing threshold.
 *  0b11..Reserved
 */
#define ADC_INTEN_ADCMPINTEN0(x)                 (((uint32_t)(((uint32_t)(x)) << ADC_INTEN_ADCMPINTEN0_SHIFT)) & ADC_INTEN_ADCMPINTEN0_MASK)
#define ADC_INTEN_ADCMPINTEN1_MASK               (0x60U)
#define ADC_INTEN_ADCMPINTEN1_SHIFT              (5U)
#define ADC_INTEN_ADCMPINTEN1(x)                 (((uint32_t)(((uint32_t)(x)) << ADC_INTEN_ADCMPINTEN1_SHIFT)) & ADC_INTEN_ADCMPINTEN1_MASK)
#define ADC_INTEN_ADCMPINTEN2_MASK               (0x180U)
#define ADC_INTEN_ADCMPINTEN2_SHIFT              (7U)
#define ADC_INTEN_ADCMPINTEN2(x)                 (((uint32_t)(((uint32_t)(x)) << ADC_INTEN_ADCMPINTEN2_SHIFT)) & ADC_INTEN_ADCMPINTEN2_MASK)
#define ADC_INTEN_ADCMPINTEN3_MASK               (0x600U)
#define ADC_INTEN_ADCMPINTEN3_SHIFT              (9U)
#define ADC_INTEN_ADCMPINTEN3(x)                 (((uint32_t)(((uint32_t)(x)) << ADC_INTEN_ADCMPINTEN3_SHIFT)) & ADC_INTEN_ADCMPINTEN3_MASK)
#define ADC_INTEN_ADCMPINTEN4_MASK               (0x1800U)
#define ADC_INTEN_ADCMPINTEN4_SHIFT              (11U)
#define ADC_INTEN_ADCMPINTEN4(x)                 (((uint32_t)(((uint32_t)(x)) << ADC_INTEN_ADCMPINTEN4_SHIFT)) & ADC_INTEN_ADCMPINTEN4_MASK)
#define ADC_INTEN_ADCMPINTEN5_MASK               (0x6000U)
#define ADC_INTEN_ADCMPINTEN5_SHIFT              (13U)
#define ADC_INTEN_ADCMPINTEN5(x)                 (((uint32_t)(((uint32_t)(x)) << ADC_INTEN_ADCMPINTEN5_SHIFT)) & ADC_INTEN_ADCMPINTEN5_MASK)
#define ADC_INTEN_ADCMPINTEN6_MASK               (0x18000U)
#define ADC_INTEN_ADCMPINTEN6_SHIFT              (15U)
#define ADC_INTEN_ADCMPINTEN6(x)                 (((uint32_t)(((uint32_t)(x)) << ADC_INTEN_ADCMPINTEN6_SHIFT)) & ADC_INTEN_ADCMPINTEN6_MASK)
#define ADC_INTEN_ADCMPINTEN7_MASK               (0x60000U)
#define ADC_INTEN_ADCMPINTEN7_SHIFT              (17U)
#define ADC_INTEN_ADCMPINTEN7(x)                 (((uint32_t)(((uint32_t)(x)) << ADC_INTEN_ADCMPINTEN7_SHIFT)) & ADC_INTEN_ADCMPINTEN7_MASK)
#define ADC_INTEN_ADCMPINTEN8_MASK               (0x180000U)
#define ADC_INTEN_ADCMPINTEN8_SHIFT              (19U)
#define ADC_INTEN_ADCMPINTEN8(x)                 (((uint32_t)(((uint32_t)(x)) << ADC_INTEN_ADCMPINTEN8_SHIFT)) & ADC_INTEN_ADCMPINTEN8_MASK)
#define ADC_INTEN_ADCMPINTEN9_MASK               (0x600000U)
#define ADC_INTEN_ADCMPINTEN9_SHIFT              (21U)
#define ADC_INTEN_ADCMPINTEN9(x)                 (((uint32_t)(((uint32_t)(x)) << ADC_INTEN_ADCMPINTEN9_SHIFT)) & ADC_INTEN_ADCMPINTEN9_MASK)
#define ADC_INTEN_ADCMPINTEN10_MASK              (0x1800000U)
#define ADC_INTEN_ADCMPINTEN10_SHIFT             (23U)
#define ADC_INTEN_ADCMPINTEN10(x)                (((uint32_t)(((uint32_t)(x)) << ADC_INTEN_ADCMPINTEN10_SHIFT)) & ADC_INTEN_ADCMPINTEN10_MASK)
#define ADC_INTEN_ADCMPINTEN11_MASK              (0x6000000U)
#define ADC_INTEN_ADCMPINTEN11_SHIFT             (25U)
#define ADC_INTEN_ADCMPINTEN11(x)                (((uint32_t)(((uint32_t)(x)) << ADC_INTEN_ADCMPINTEN11_SHIFT)) & ADC_INTEN_ADCMPINTEN11_MASK)
/*! @} */

/*! @name FLAGS - ADC Flags register. Contains the four interrupt/DMA trigger flags and the individual component overrun and threshold-compare flags. (The overrun bits replicate information stored in the result registers). */
/*! @{ */
#define ADC_FLAGS_THCMP0_MASK                    (0x1U)
#define ADC_FLAGS_THCMP0_SHIFT                   (0U)
#define ADC_FLAGS_THCMP0(x)                      (((uint32_t)(((uint32_t)(x)) << ADC_FLAGS_THCMP0_SHIFT)) & ADC_FLAGS_THCMP0_MASK)
#define ADC_FLAGS_THCMP1_MASK                    (0x2U)
#define ADC_FLAGS_THCMP1_SHIFT                   (1U)
#define ADC_FLAGS_THCMP1(x)                      (((uint32_t)(((uint32_t)(x)) << ADC_FLAGS_THCMP1_SHIFT)) & ADC_FLAGS_THCMP1_MASK)
#define ADC_FLAGS_THCMP2_MASK                    (0x4U)
#define ADC_FLAGS_THCMP2_SHIFT                   (2U)
#define ADC_FLAGS_THCMP2(x)                      (((uint32_t)(((uint32_t)(x)) << ADC_FLAGS_THCMP2_SHIFT)) & ADC_FLAGS_THCMP2_MASK)
#define ADC_FLAGS_THCMP3_MASK                    (0x8U)
#define ADC_FLAGS_THCMP3_SHIFT                   (3U)
#define ADC_FLAGS_THCMP3(x)                      (((uint32_t)(((uint32_t)(x)) << ADC_FLAGS_THCMP3_SHIFT)) & ADC_FLAGS_THCMP3_MASK)
#define ADC_FLAGS_THCMP4_MASK                    (0x10U)
#define ADC_FLAGS_THCMP4_SHIFT                   (4U)
#define ADC_FLAGS_THCMP4(x)                      (((uint32_t)(((uint32_t)(x)) << ADC_FLAGS_THCMP4_SHIFT)) & ADC_FLAGS_THCMP4_MASK)
#define ADC_FLAGS_THCMP5_MASK                    (0x20U)
#define ADC_FLAGS_THCMP5_SHIFT                   (5U)
#define ADC_FLAGS_THCMP5(x)                      (((uint32_t)(((uint32_t)(x)) << ADC_FLAGS_THCMP5_SHIFT)) & ADC_FLAGS_THCMP5_MASK)
#define ADC_FLAGS_THCMP6_MASK                    (0x40U)
#define ADC_FLAGS_THCMP6_SHIFT                   (6U)
#define ADC_FLAGS_THCMP6(x)                      (((uint32_t)(((uint32_t)(x)) << ADC_FLAGS_THCMP6_SHIFT)) & ADC_FLAGS_THCMP6_MASK)
#define ADC_FLAGS_THCMP7_MASK                    (0x80U)
#define ADC_FLAGS_THCMP7_SHIFT                   (7U)
#define ADC_FLAGS_THCMP7(x)                      (((uint32_t)(((uint32_t)(x)) << ADC_FLAGS_THCMP7_SHIFT)) & ADC_FLAGS_THCMP7_MASK)
#define ADC_FLAGS_THCMP8_MASK                    (0x100U)
#define ADC_FLAGS_THCMP8_SHIFT                   (8U)
#define ADC_FLAGS_THCMP8(x)                      (((uint32_t)(((uint32_t)(x)) << ADC_FLAGS_THCMP8_SHIFT)) & ADC_FLAGS_THCMP8_MASK)
#define ADC_FLAGS_THCMP9_MASK                    (0x200U)
#define ADC_FLAGS_THCMP9_SHIFT                   (9U)
#define ADC_FLAGS_THCMP9(x)                      (((uint32_t)(((uint32_t)(x)) << ADC_FLAGS_THCMP9_SHIFT)) & ADC_FLAGS_THCMP9_MASK)
#define ADC_FLAGS_THCMP10_MASK                   (0x400U)
#define ADC_FLAGS_THCMP10_SHIFT                  (10U)
#define ADC_FLAGS_THCMP10(x)                     (((uint32_t)(((uint32_t)(x)) << ADC_FLAGS_THCMP10_SHIFT)) & ADC_FLAGS_THCMP10_MASK)
#define ADC_FLAGS_THCMP11_MASK                   (0x800U)
#define ADC_FLAGS_THCMP11_SHIFT                  (11U)
#define ADC_FLAGS_THCMP11(x)                     (((uint32_t)(((uint32_t)(x)) << ADC_FLAGS_THCMP11_SHIFT)) & ADC_FLAGS_THCMP11_MASK)
#define ADC_FLAGS_OVERRUN0_MASK                  (0x1000U)
#define ADC_FLAGS_OVERRUN0_SHIFT                 (12U)
#define ADC_FLAGS_OVERRUN0(x)                    (((uint32_t)(((uint32_t)(x)) << ADC_FLAGS_OVERRUN0_SHIFT)) & ADC_FLAGS_OVERRUN0_MASK)
#define ADC_FLAGS_OVERRUN1_MASK                  (0x2000U)
#define ADC_FLAGS_OVERRUN1_SHIFT                 (13U)
#define ADC_FLAGS_OVERRUN1(x)                    (((uint32_t)(((uint32_t)(x)) << ADC_FLAGS_OVERRUN1_SHIFT)) & ADC_FLAGS_OVERRUN1_MASK)
#define ADC_FLAGS_OVERRUN2_MASK                  (0x4000U)
#define ADC_FLAGS_OVERRUN2_SHIFT                 (14U)
#define ADC_FLAGS_OVERRUN2(x)                    (((uint32_t)(((uint32_t)(x)) << ADC_FLAGS_OVERRUN2_SHIFT)) & ADC_FLAGS_OVERRUN2_MASK)
#define ADC_FLAGS_OVERRUN3_MASK                  (0x8000U)
#define ADC_FLAGS_OVERRUN3_SHIFT                 (15U)
#define ADC_FLAGS_OVERRUN3(x)                    (((uint32_t)(((uint32_t)(x)) << ADC_FLAGS_OVERRUN3_SHIFT)) & ADC_FLAGS_OVERRUN3_MASK)
#define ADC_FLAGS_OVERRUN4_MASK                  (0x10000U)
#define ADC_FLAGS_OVERRUN4_SHIFT                 (16U)
#define ADC_FLAGS_OVERRUN4(x)                    (((uint32_t)(((uint32_t)(x)) << ADC_FLAGS_OVERRUN4_SHIFT)) & ADC_FLAGS_OVERRUN4_MASK)
#define ADC_FLAGS_OVERRUN5_MASK                  (0x20000U)
#define ADC_FLAGS_OVERRUN5_SHIFT                 (17U)
#define ADC_FLAGS_OVERRUN5(x)                    (((uint32_t)(((uint32_t)(x)) << ADC_FLAGS_OVERRUN5_SHIFT)) & ADC_FLAGS_OVERRUN5_MASK)
#define ADC_FLAGS_OVERRUN6_MASK                  (0x40000U)
#define ADC_FLAGS_OVERRUN6_SHIFT                 (18U)
#define ADC_FLAGS_OVERRUN6(x)                    (((uint32_t)(((uint32_t)(x)) << ADC_FLAGS_OVERRUN6_SHIFT)) & ADC_FLAGS_OVERRUN6_MASK)
#define ADC_FLAGS_OVERRUN7_MASK                  (0x80000U)
#define ADC_FLAGS_OVERRUN7_SHIFT                 (19U)
#define ADC_FLAGS_OVERRUN7(x)                    (((uint32_t)(((uint32_t)(x)) << ADC_FLAGS_OVERRUN7_SHIFT)) & ADC_FLAGS_OVERRUN7_MASK)
#define ADC_FLAGS_OVERRUN8_MASK                  (0x100000U)
#define ADC_FLAGS_OVERRUN8_SHIFT                 (20U)
#define ADC_FLAGS_OVERRUN8(x)                    (((uint32_t)(((uint32_t)(x)) << ADC_FLAGS_OVERRUN8_SHIFT)) & ADC_FLAGS_OVERRUN8_MASK)
#define ADC_FLAGS_OVERRUN9_MASK                  (0x200000U)
#define ADC_FLAGS_OVERRUN9_SHIFT                 (21U)
#define ADC_FLAGS_OVERRUN9(x)                    (((uint32_t)(((uint32_t)(x)) << ADC_FLAGS_OVERRUN9_SHIFT)) & ADC_FLAGS_OVERRUN9_MASK)
#define ADC_FLAGS_OVERRUN10_MASK                 (0x400000U)
#define ADC_FLAGS_OVERRUN10_SHIFT                (22U)
#define ADC_FLAGS_OVERRUN10(x)                   (((uint32_t)(((uint32_t)(x)) << ADC_FLAGS_OVERRUN10_SHIFT)) & ADC_FLAGS_OVERRUN10_MASK)
#define ADC_FLAGS_OVERRUN11_MASK                 (0x800000U)
#define ADC_FLAGS_OVERRUN11_SHIFT                (23U)
#define ADC_FLAGS_OVERRUN11(x)                   (((uint32_t)(((uint32_t)(x)) << ADC_FLAGS_OVERRUN11_SHIFT)) & ADC_FLAGS_OVERRUN11_MASK)
#define ADC_FLAGS_SEQA_OVR_MASK                  (0x1000000U)
#define ADC_FLAGS_SEQA_OVR_SHIFT                 (24U)
#define ADC_FLAGS_SEQA_OVR(x)                    (((uint32_t)(((uint32_t)(x)) << ADC_FLAGS_SEQA_OVR_SHIFT)) & ADC_FLAGS_SEQA_OVR_MASK)
#define ADC_FLAGS_SEQB_OVR_MASK                  (0x2000000U)
#define ADC_FLAGS_SEQB_OVR_SHIFT                 (25U)
#define ADC_FLAGS_SEQB_OVR(x)                    (((uint32_t)(((uint32_t)(x)) << ADC_FLAGS_SEQB_OVR_SHIFT)) & ADC_FLAGS_SEQB_OVR_MASK)
#define ADC_FLAGS_SEQA_INT_MASK                  (0x10000000U)
#define ADC_FLAGS_SEQA_INT_SHIFT                 (28U)
#define ADC_FLAGS_SEQA_INT(x)                    (((uint32_t)(((uint32_t)(x)) << ADC_FLAGS_SEQA_INT_SHIFT)) & ADC_FLAGS_SEQA_INT_MASK)
#define ADC_FLAGS_SEQB_INT_MASK                  (0x20000000U)
#define ADC_FLAGS_SEQB_INT_SHIFT                 (29U)
#define ADC_FLAGS_SEQB_INT(x)                    (((uint32_t)(((uint32_t)(x)) << ADC_FLAGS_SEQB_INT_SHIFT)) & ADC_FLAGS_SEQB_INT_MASK)
#define ADC_FLAGS_THCMP_INT_MASK                 (0x40000000U)
#define ADC_FLAGS_THCMP_INT_SHIFT                (30U)
#define ADC_FLAGS_THCMP_INT(x)                   (((uint32_t)(((uint32_t)(x)) << ADC_FLAGS_THCMP_INT_SHIFT)) & ADC_FLAGS_THCMP_INT_MASK)
#define ADC_FLAGS_OVR_INT_MASK                   (0x80000000U)
#define ADC_FLAGS_OVR_INT_SHIFT                  (31U)
#define ADC_FLAGS_OVR_INT(x)                     (((uint32_t)(((uint32_t)(x)) << ADC_FLAGS_OVR_INT_SHIFT)) & ADC_FLAGS_OVR_INT_MASK)
/*! @} */


/*!
 * @}
 */ /* end of group ADC_Register_Masks */


/* ADC - Peripheral instance base addresses */
/** Peripheral ADC base address */
#define ADC_BASE                                 (0x4001C000u)
/** Peripheral ADC base pointer */
#define ADC                                      ((ADC_Type *)ADC_BASE)
/** Array initializer of ADC peripheral base addresses */
#define ADC_BASE_ADDRS                           { ADC_BASE }
/** Array initializer of ADC peripheral base pointers */
#define ADC_BASE_PTRS                            { ADC }
/** Interrupt vectors for the ADC peripheral type */
#define ADC_SEQ_IRQS                             { ADC_SEQA_IRQn, ADC_SEQB_IRQn }
#define ADC_THCMP_IRQS                           { ADC_THCMP_IRQn }

/*!
 * @}
 */ /* end of group ADC_Peripheral_Access_Layer */


/* ----------------------------------------------------------------------------
   -- CAPT Peripheral Access Layer
   ---------------------------------------------------------------------------- */

/*!
 * @addtogroup CAPT_Peripheral_Access_Layer CAPT Peripheral Access Layer
 * @{
 */

/** CAPT - Register Layout Typedef */
typedef struct {
  __IO uint32_t CTRL;                              /**< Configuration and control to setup the functional clock, the rules, and the pin selections and rules., offset: 0x0 */
  __IO uint32_t STATUS;                            /**< Status from triggers and time-outs including if in a poll now. Some are used for interrupts., offset: 0x4 */
  __IO uint32_t POLL_TCNT;                         /**< This sets up the polling counter and measurement counter rules., offset: 0x8 */
       uint8_t RESERVED_0[4];
  __IO uint32_t INTENSET;                          /**< Interrupt enable, offset: 0x10 */
  __IO uint32_t INTENCLR;                          /**< Interrupt enable clear, offset: 0x14 */
  __I  uint32_t INTSTAT;                           /**< Interrupt status (mask of STATUS and INTEN), offset: 0x18 */
       uint8_t RESERVED_1[4];
  __I  uint32_t TOUCH;                             /**< Last touch event (touch or no-touch) in context., offset: 0x20 */
       uint8_t RESERVED_2[4056];
  __I  uint32_t ID;                                /**< Block ID., offset: 0xFFC */
} CAPT_Type;

/* ----------------------------------------------------------------------------
   -- CAPT Register Masks
   ---------------------------------------------------------------------------- */

/*!
 * @addtogroup CAPT_Register_Masks CAPT Register Masks
 * @{
 */

/*! @name CTRL - Configuration and control to setup the functional clock, the rules, and the pin selections and rules. */
/*! @{ */
#define CAPT_CTRL_POLLMODE_MASK                  (0x3U)
#define CAPT_CTRL_POLLMODE_SHIFT                 (0U)
/*! POLLMODE - Mode of operation. May only change from 0 to another value. So, if 2 or 3, must be
 *    changed to 0 1st. Any attempt to go from non-0 to non-0 will result in 0 anyway.
 *  0b00..None, inactive. Poll and time counters are turned off. Writing this will reset state and stop any
 *        collection in progress. Note: this has no effect on STATUS - those must be cleared manually.
 *  0b01..Poll now - forces a manual poll to be started immediately, using XPINSEL X pin(s) to activate in the
 *        integration loop (all pins set together). Self clears - clear is not indication it is done (see STATUS).
 *  0b10..Normal polling using poll delay from POLL_TCNT register. This will start with the poll delay (which can be 0).
 *  0b11..The CAPT block will operate in low-power mode. This means it will use GPIO as input, use combination
 *        touch measurements, and assume it is to wake the system. This will use the POLL_TCNT poll delay, and start
 *        with the delay.
 */
#define CAPT_CTRL_POLLMODE(x)                    (((uint32_t)(((uint32_t)(x)) << CAPT_CTRL_POLLMODE_SHIFT)) & CAPT_CTRL_POLLMODE_MASK)
#define CAPT_CTRL_TYPE_MASK                      (0xCU)
#define CAPT_CTRL_TYPE_SHIFT                     (2U)
/*! TYPE - Selects type of Touch arrangement to use and so how to handle XPINSEL bits
 *  0b00..Normal - all X elements are treated as normal, such as buttons and sliders.
 *  0b01..3x3 grid using NXP Complementary measurements. The 1st 9 Xs are assumed to be the 3x3 grid. After that
 *        would be normal X elements. This will also allow 3x1 and 3x2 Note: Only possible if XMAX in STATUS is >=8
 *  0b10..5 Sensors interleaved to act as 3x3 touch area using NXP Complementary measurements. 1st 5 Xs used for
 *        this, all remaining are treated as normal. Note that if 16 X pins allowed, the 16th will not be usable
 *        when TYPE=1. (use TYPE=0 and select 1 smaller than 15 ( and any others from 1 smaller than 5 on up in
 *        XPINSEL).
 *  0b11..9 Sensors interleaved to act as 5x5 touch area using NXP Complementary measurements. 1st 9 Xs used for
 *        this, all remaining are treated as normal. Note: Only possible if XMAX in STATUS is >=8
 */
#define CAPT_CTRL_TYPE(x)                        (((uint32_t)(((uint32_t)(x)) << CAPT_CTRL_TYPE_SHIFT)) & CAPT_CTRL_TYPE_MASK)
#define CAPT_CTRL_TRIGGER_MASK                   (0x10U)
#define CAPT_CTRL_TRIGGER_SHIFT                  (4U)
/*! TRIGGER - This selects what is being used as the trigger
 *  0b0..Uses YH GPIO. This is not normally used except in Low-power mode. But, it can be used with POLLNOW to baseline that measurement.
 *  0b1..ACMP (if fitted). This assumes the ACMP state is fed in asynchronously and it will sample.
 */
#define CAPT_CTRL_TRIGGER(x)                     (((uint32_t)(((uint32_t)(x)) << CAPT_CTRL_TRIGGER_SHIFT)) & CAPT_CTRL_TRIGGER_MASK)
#define CAPT_CTRL_WAIT_MASK                      (0x20U)
#define CAPT_CTRL_WAIT_SHIFT                     (5U)
#define CAPT_CTRL_WAIT(x)                        (((uint32_t)(((uint32_t)(x)) << CAPT_CTRL_WAIT_SHIFT)) & CAPT_CTRL_WAIT_MASK)
#define CAPT_CTRL_FDIV_MASK                      (0xF00U)
#define CAPT_CTRL_FDIV_SHIFT                     (8U)
/*! FDIV - Functional clock divider, or 0 if no divide. The term "clocks" in this spec then refer to
 *    divided clocks. For a 12MHz input (e.g. FRO 12MHz), this would normally be set to generate a
 *    4MHz output (so, 2). For a 1MHz input, it should be 0. Note for internal use: this does not
 *    produce a 50/50 duty cycle when non even divide.
 *  0b0000..No divide
 *  0b0001../2
 *  0b0010../3
 *  0b0011../4
 *  0b0100../5
 *  0b0101../6
 *  0b0111../(FDIV+1)
 *  0b1000../(FDIV+1)
 *  0b1001../(FDIV+1)
 *  0b1010../(FDIV+1)
 *  0b1011../(FDIV+1)
 *  0b1100../(FDIV+1)
 *  0b1101../(FDIV+1)
 *  0b1110../(FDIV+1)
 *  0b1111../(FDIV+1)
 */
#define CAPT_CTRL_FDIV(x)                        (((uint32_t)(((uint32_t)(x)) << CAPT_CTRL_FDIV_SHIFT)) & CAPT_CTRL_FDIV_MASK)
#define CAPT_CTRL_XPINUSE_MASK                   (0x3000U)
#define CAPT_CTRL_XPINUSE_SHIFT                  (12U)
/*! XPINUSE - Controls how X pins selected in XPINSEL are used when not active in the current polling round.
 *  0b00..Normal mode. Each inactive X pin is Hi-Z.
 *  0b01..Ground mode. Each inactive X pin is Low
 */
#define CAPT_CTRL_XPINUSE(x)                     (((uint32_t)(((uint32_t)(x)) << CAPT_CTRL_XPINUSE_SHIFT)) & CAPT_CTRL_XPINUSE_MASK)
#define CAPT_CTRL_INCHANGE_MASK                  (0x8000U)
#define CAPT_CTRL_INCHANGE_SHIFT                 (15U)
#define CAPT_CTRL_INCHANGE(x)                    (((uint32_t)(((uint32_t)(x)) << CAPT_CTRL_INCHANGE_SHIFT)) & CAPT_CTRL_INCHANGE_MASK)
#define CAPT_CTRL_XPINSEL_MASK                   (0xFFFF0000U)
#define CAPT_CTRL_XPINSEL_SHIFT                  (16U)
#define CAPT_CTRL_XPINSEL(x)                     (((uint32_t)(((uint32_t)(x)) << CAPT_CTRL_XPINSEL_SHIFT)) & CAPT_CTRL_XPINSEL_MASK)
/*! @} */

/*! @name STATUS - Status from triggers and time-outs including if in a poll now. Some are used for interrupts. */
/*! @{ */
#define CAPT_STATUS_YESTOUCH_MASK                (0x1U)
#define CAPT_STATUS_YESTOUCH_SHIFT               (0U)
#define CAPT_STATUS_YESTOUCH(x)                  (((uint32_t)(((uint32_t)(x)) << CAPT_STATUS_YESTOUCH_SHIFT)) & CAPT_STATUS_YESTOUCH_MASK)
#define CAPT_STATUS_NOTOUCH_MASK                 (0x2U)
#define CAPT_STATUS_NOTOUCH_SHIFT                (1U)
#define CAPT_STATUS_NOTOUCH(x)                   (((uint32_t)(((uint32_t)(x)) << CAPT_STATUS_NOTOUCH_SHIFT)) & CAPT_STATUS_NOTOUCH_MASK)
#define CAPT_STATUS_POLLDONE_MASK                (0x4U)
#define CAPT_STATUS_POLLDONE_SHIFT               (2U)
#define CAPT_STATUS_POLLDONE(x)                  (((uint32_t)(((uint32_t)(x)) << CAPT_STATUS_POLLDONE_SHIFT)) & CAPT_STATUS_POLLDONE_MASK)
#define CAPT_STATUS_TIMEOUT_MASK                 (0x8U)
#define CAPT_STATUS_TIMEOUT_SHIFT                (3U)
#define CAPT_STATUS_TIMEOUT(x)                   (((uint32_t)(((uint32_t)(x)) << CAPT_STATUS_TIMEOUT_SHIFT)) & CAPT_STATUS_TIMEOUT_MASK)
#define CAPT_STATUS_OVERUN_MASK                  (0x10U)
#define CAPT_STATUS_OVERUN_SHIFT                 (4U)
#define CAPT_STATUS_OVERUN(x)                    (((uint32_t)(((uint32_t)(x)) << CAPT_STATUS_OVERUN_SHIFT)) & CAPT_STATUS_OVERUN_MASK)
#define CAPT_STATUS_BUSY_MASK                    (0x100U)
#define CAPT_STATUS_BUSY_SHIFT                   (8U)
#define CAPT_STATUS_BUSY(x)                      (((uint32_t)(((uint32_t)(x)) << CAPT_STATUS_BUSY_SHIFT)) & CAPT_STATUS_BUSY_MASK)
#define CAPT_STATUS_XMAX_MASK                    (0xF0000U)
#define CAPT_STATUS_XMAX_SHIFT                   (16U)
#define CAPT_STATUS_XMAX(x)                      (((uint32_t)(((uint32_t)(x)) << CAPT_STATUS_XMAX_SHIFT)) & CAPT_STATUS_XMAX_MASK)
/*! @} */

/*! @name POLL_TCNT - This sets up the polling counter and measurement counter rules. */
/*! @{ */
#define CAPT_POLL_TCNT_TCNT_MASK                 (0xFFFU)
#define CAPT_POLL_TCNT_TCNT_SHIFT                (0U)
#define CAPT_POLL_TCNT_TCNT(x)                   (((uint32_t)(((uint32_t)(x)) << CAPT_POLL_TCNT_TCNT_SHIFT)) & CAPT_POLL_TCNT_TCNT_MASK)
#define CAPT_POLL_TCNT_TOUT_MASK                 (0xF000U)
#define CAPT_POLL_TCNT_TOUT_SHIFT                (12U)
#define CAPT_POLL_TCNT_TOUT(x)                   (((uint32_t)(((uint32_t)(x)) << CAPT_POLL_TCNT_TOUT_SHIFT)) & CAPT_POLL_TCNT_TOUT_MASK)
#define CAPT_POLL_TCNT_POLL_MASK                 (0xFF0000U)
#define CAPT_POLL_TCNT_POLL_SHIFT                (16U)
#define CAPT_POLL_TCNT_POLL(x)                   (((uint32_t)(((uint32_t)(x)) << CAPT_POLL_TCNT_POLL_SHIFT)) & CAPT_POLL_TCNT_POLL_MASK)
#define CAPT_POLL_TCNT_MDELAY_MASK               (0x3000000U)
#define CAPT_POLL_TCNT_MDELAY_SHIFT              (24U)
#define CAPT_POLL_TCNT_MDELAY(x)                 (((uint32_t)(((uint32_t)(x)) << CAPT_POLL_TCNT_MDELAY_SHIFT)) & CAPT_POLL_TCNT_MDELAY_MASK)
#define CAPT_POLL_TCNT_RDELAY_MASK               (0xC000000U)
#define CAPT_POLL_TCNT_RDELAY_SHIFT              (26U)
#define CAPT_POLL_TCNT_RDELAY(x)                 (((uint32_t)(((uint32_t)(x)) << CAPT_POLL_TCNT_RDELAY_SHIFT)) & CAPT_POLL_TCNT_RDELAY_MASK)
#define CAPT_POLL_TCNT_TCHLOW_ER_MASK            (0x80000000U)
#define CAPT_POLL_TCNT_TCHLOW_ER_SHIFT           (31U)
#define CAPT_POLL_TCNT_TCHLOW_ER(x)              (((uint32_t)(((uint32_t)(x)) << CAPT_POLL_TCNT_TCHLOW_ER_SHIFT)) & CAPT_POLL_TCNT_TCHLOW_ER_MASK)
/*! @} */

/*! @name INTENSET - Interrupt enable */
/*! @{ */
#define CAPT_INTENSET_YESTOUCH_MASK              (0x1U)
#define CAPT_INTENSET_YESTOUCH_SHIFT             (0U)
#define CAPT_INTENSET_YESTOUCH(x)                (((uint32_t)(((uint32_t)(x)) << CAPT_INTENSET_YESTOUCH_SHIFT)) & CAPT_INTENSET_YESTOUCH_MASK)
#define CAPT_INTENSET_NOTOUCH_MASK               (0x2U)
#define CAPT_INTENSET_NOTOUCH_SHIFT              (1U)
#define CAPT_INTENSET_NOTOUCH(x)                 (((uint32_t)(((uint32_t)(x)) << CAPT_INTENSET_NOTOUCH_SHIFT)) & CAPT_INTENSET_NOTOUCH_MASK)
#define CAPT_INTENSET_POLLDONE_MASK              (0x4U)
#define CAPT_INTENSET_POLLDONE_SHIFT             (2U)
#define CAPT_INTENSET_POLLDONE(x)                (((uint32_t)(((uint32_t)(x)) << CAPT_INTENSET_POLLDONE_SHIFT)) & CAPT_INTENSET_POLLDONE_MASK)
#define CAPT_INTENSET_TIMEOUT_MASK               (0x8U)
#define CAPT_INTENSET_TIMEOUT_SHIFT              (3U)
#define CAPT_INTENSET_TIMEOUT(x)                 (((uint32_t)(((uint32_t)(x)) << CAPT_INTENSET_TIMEOUT_SHIFT)) & CAPT_INTENSET_TIMEOUT_MASK)
#define CAPT_INTENSET_OVERUN_MASK                (0x10U)
#define CAPT_INTENSET_OVERUN_SHIFT               (4U)
#define CAPT_INTENSET_OVERUN(x)                  (((uint32_t)(((uint32_t)(x)) << CAPT_INTENSET_OVERUN_SHIFT)) & CAPT_INTENSET_OVERUN_MASK)
/*! @} */

/*! @name INTENCLR - Interrupt enable clear */
/*! @{ */
#define CAPT_INTENCLR_YESTOUCH_MASK              (0x1U)
#define CAPT_INTENCLR_YESTOUCH_SHIFT             (0U)
#define CAPT_INTENCLR_YESTOUCH(x)                (((uint32_t)(((uint32_t)(x)) << CAPT_INTENCLR_YESTOUCH_SHIFT)) & CAPT_INTENCLR_YESTOUCH_MASK)
#define CAPT_INTENCLR_NOTOUCH_MASK               (0x2U)
#define CAPT_INTENCLR_NOTOUCH_SHIFT              (1U)
#define CAPT_INTENCLR_NOTOUCH(x)                 (((uint32_t)(((uint32_t)(x)) << CAPT_INTENCLR_NOTOUCH_SHIFT)) & CAPT_INTENCLR_NOTOUCH_MASK)
#define CAPT_INTENCLR_POLLDONE_MASK              (0x4U)
#define CAPT_INTENCLR_POLLDONE_SHIFT             (2U)
#define CAPT_INTENCLR_POLLDONE(x)                (((uint32_t)(((uint32_t)(x)) << CAPT_INTENCLR_POLLDONE_SHIFT)) & CAPT_INTENCLR_POLLDONE_MASK)
#define CAPT_INTENCLR_TIMEOUT_MASK               (0x8U)
#define CAPT_INTENCLR_TIMEOUT_SHIFT              (3U)
#define CAPT_INTENCLR_TIMEOUT(x)                 (((uint32_t)(((uint32_t)(x)) << CAPT_INTENCLR_TIMEOUT_SHIFT)) & CAPT_INTENCLR_TIMEOUT_MASK)
#define CAPT_INTENCLR_OVERUN_MASK                (0x10U)
#define CAPT_INTENCLR_OVERUN_SHIFT               (4U)
#define CAPT_INTENCLR_OVERUN(x)                  (((uint32_t)(((uint32_t)(x)) << CAPT_INTENCLR_OVERUN_SHIFT)) & CAPT_INTENCLR_OVERUN_MASK)
/*! @} */

/*! @name INTSTAT - Interrupt status (mask of STATUS and INTEN) */
/*! @{ */
#define CAPT_INTSTAT_YESTOUCH_MASK               (0x1U)
#define CAPT_INTSTAT_YESTOUCH_SHIFT              (0U)
#define CAPT_INTSTAT_YESTOUCH(x)                 (((uint32_t)(((uint32_t)(x)) << CAPT_INTSTAT_YESTOUCH_SHIFT)) & CAPT_INTSTAT_YESTOUCH_MASK)
#define CAPT_INTSTAT_NOTOUCH_MASK                (0x2U)
#define CAPT_INTSTAT_NOTOUCH_SHIFT               (1U)
#define CAPT_INTSTAT_NOTOUCH(x)                  (((uint32_t)(((uint32_t)(x)) << CAPT_INTSTAT_NOTOUCH_SHIFT)) & CAPT_INTSTAT_NOTOUCH_MASK)
#define CAPT_INTSTAT_POLLDONE_MASK               (0x4U)
#define CAPT_INTSTAT_POLLDONE_SHIFT              (2U)
#define CAPT_INTSTAT_POLLDONE(x)                 (((uint32_t)(((uint32_t)(x)) << CAPT_INTSTAT_POLLDONE_SHIFT)) & CAPT_INTSTAT_POLLDONE_MASK)
#define CAPT_INTSTAT_TIMEOUT_MASK                (0x8U)
#define CAPT_INTSTAT_TIMEOUT_SHIFT               (3U)
#define CAPT_INTSTAT_TIMEOUT(x)                  (((uint32_t)(((uint32_t)(x)) << CAPT_INTSTAT_TIMEOUT_SHIFT)) & CAPT_INTSTAT_TIMEOUT_MASK)
#define CAPT_INTSTAT_OVERUN_MASK                 (0x10U)
#define CAPT_INTSTAT_OVERUN_SHIFT                (4U)
#define CAPT_INTSTAT_OVERUN(x)                   (((uint32_t)(((uint32_t)(x)) << CAPT_INTSTAT_OVERUN_SHIFT)) & CAPT_INTSTAT_OVERUN_MASK)
/*! @} */

/*! @name TOUCH - Last touch event (touch or no-touch) in context. */
/*! @{ */
#define CAPT_TOUCH_COUNT_MASK                    (0xFFFU)
#define CAPT_TOUCH_COUNT_SHIFT                   (0U)
#define CAPT_TOUCH_COUNT(x)                      (((uint32_t)(((uint32_t)(x)) << CAPT_TOUCH_COUNT_SHIFT)) & CAPT_TOUCH_COUNT_MASK)
#define CAPT_TOUCH_XVAL_MASK                     (0xF000U)
#define CAPT_TOUCH_XVAL_SHIFT                    (12U)
#define CAPT_TOUCH_XVAL(x)                       (((uint32_t)(((uint32_t)(x)) << CAPT_TOUCH_XVAL_SHIFT)) & CAPT_TOUCH_XVAL_MASK)
#define CAPT_TOUCH_ISTOUCH_MASK                  (0x10000U)
#define CAPT_TOUCH_ISTOUCH_SHIFT                 (16U)
#define CAPT_TOUCH_ISTOUCH(x)                    (((uint32_t)(((uint32_t)(x)) << CAPT_TOUCH_ISTOUCH_SHIFT)) & CAPT_TOUCH_ISTOUCH_MASK)
#define CAPT_TOUCH_ISTO_MASK                     (0x20000U)
#define CAPT_TOUCH_ISTO_SHIFT                    (17U)
#define CAPT_TOUCH_ISTO(x)                       (((uint32_t)(((uint32_t)(x)) << CAPT_TOUCH_ISTO_SHIFT)) & CAPT_TOUCH_ISTO_MASK)
#define CAPT_TOUCH_SEQ_MASK                      (0xF00000U)
#define CAPT_TOUCH_SEQ_SHIFT                     (20U)
#define CAPT_TOUCH_SEQ(x)                        (((uint32_t)(((uint32_t)(x)) << CAPT_TOUCH_SEQ_SHIFT)) & CAPT_TOUCH_SEQ_MASK)
#define CAPT_TOUCH_CHANGE_MASK                   (0x80000000U)
#define CAPT_TOUCH_CHANGE_SHIFT                  (31U)
#define CAPT_TOUCH_CHANGE(x)                     (((uint32_t)(((uint32_t)(x)) << CAPT_TOUCH_CHANGE_SHIFT)) & CAPT_TOUCH_CHANGE_MASK)
/*! @} */

/*! @name ID - Block ID. */
/*! @{ */
#define CAPT_ID_APERTURE_MASK                    (0xFFU)
#define CAPT_ID_APERTURE_SHIFT                   (0U)
#define CAPT_ID_APERTURE(x)                      (((uint32_t)(((uint32_t)(x)) << CAPT_ID_APERTURE_SHIFT)) & CAPT_ID_APERTURE_MASK)
#define CAPT_ID_MINOR_REV_MASK                   (0xF00U)
#define CAPT_ID_MINOR_REV_SHIFT                  (8U)
#define CAPT_ID_MINOR_REV(x)                     (((uint32_t)(((uint32_t)(x)) << CAPT_ID_MINOR_REV_SHIFT)) & CAPT_ID_MINOR_REV_MASK)
#define CAPT_ID_MAJOR_REV_MASK                   (0xF000U)
#define CAPT_ID_MAJOR_REV_SHIFT                  (12U)
#define CAPT_ID_MAJOR_REV(x)                     (((uint32_t)(((uint32_t)(x)) << CAPT_ID_MAJOR_REV_SHIFT)) & CAPT_ID_MAJOR_REV_MASK)
#define CAPT_ID_ID_MASK                          (0xFFFF0000U)
#define CAPT_ID_ID_SHIFT                         (16U)
#define CAPT_ID_ID(x)                            (((uint32_t)(((uint32_t)(x)) << CAPT_ID_ID_SHIFT)) & CAPT_ID_ID_MASK)
/*! @} */


/*!
 * @}
 */ /* end of group CAPT_Register_Masks */


/* CAPT - Peripheral instance base addresses */
/** Peripheral CAPT base address */
#define CAPT_BASE                                (0x40060000u)
/** Peripheral CAPT base pointer */
#define CAPT                                     ((CAPT_Type *)CAPT_BASE)
/** Array initializer of CAPT peripheral base addresses */
#define CAPT_BASE_ADDRS                          { CAPT_BASE }
/** Array initializer of CAPT peripheral base pointers */
#define CAPT_BASE_PTRS                           { CAPT }

/*!
 * @}
 */ /* end of group CAPT_Peripheral_Access_Layer */


/* ----------------------------------------------------------------------------
   -- CRC Peripheral Access Layer
   ---------------------------------------------------------------------------- */

/*!
 * @addtogroup CRC_Peripheral_Access_Layer CRC Peripheral Access Layer
 * @{
 */

/** CRC - Register Layout Typedef */
typedef struct {
  __IO uint32_t MODE;                              /**< CRC mode register, offset: 0x0 */
  __IO uint32_t SEED;                              /**< CRC seed register, offset: 0x4 */
  union {                                          /* offset: 0x8 */
    __I  uint32_t SUM;                               /**< CRC checksum register, offset: 0x8 */
    __O  uint32_t WR_DATA;                           /**< CRC data register, offset: 0x8 */
  };
} CRC_Type;

/* ----------------------------------------------------------------------------
   -- CRC Register Masks
   ---------------------------------------------------------------------------- */

/*!
 * @addtogroup CRC_Register_Masks CRC Register Masks
 * @{
 */

/*! @name MODE - CRC mode register */
/*! @{ */
#define CRC_MODE_CRC_POLY_MASK                   (0x3U)
#define CRC_MODE_CRC_POLY_SHIFT                  (0U)
#define CRC_MODE_CRC_POLY(x)                     (((uint32_t)(((uint32_t)(x)) << CRC_MODE_CRC_POLY_SHIFT)) & CRC_MODE_CRC_POLY_MASK)
#define CRC_MODE_BIT_RVS_WR_MASK                 (0x4U)
#define CRC_MODE_BIT_RVS_WR_SHIFT                (2U)
#define CRC_MODE_BIT_RVS_WR(x)                   (((uint32_t)(((uint32_t)(x)) << CRC_MODE_BIT_RVS_WR_SHIFT)) & CRC_MODE_BIT_RVS_WR_MASK)
#define CRC_MODE_CMPL_WR_MASK                    (0x8U)
#define CRC_MODE_CMPL_WR_SHIFT                   (3U)
#define CRC_MODE_CMPL_WR(x)                      (((uint32_t)(((uint32_t)(x)) << CRC_MODE_CMPL_WR_SHIFT)) & CRC_MODE_CMPL_WR_MASK)
#define CRC_MODE_BIT_RVS_SUM_MASK                (0x10U)
#define CRC_MODE_BIT_RVS_SUM_SHIFT               (4U)
#define CRC_MODE_BIT_RVS_SUM(x)                  (((uint32_t)(((uint32_t)(x)) << CRC_MODE_BIT_RVS_SUM_SHIFT)) & CRC_MODE_BIT_RVS_SUM_MASK)
#define CRC_MODE_CMPL_SUM_MASK                   (0x20U)
#define CRC_MODE_CMPL_SUM_SHIFT                  (5U)
#define CRC_MODE_CMPL_SUM(x)                     (((uint32_t)(((uint32_t)(x)) << CRC_MODE_CMPL_SUM_SHIFT)) & CRC_MODE_CMPL_SUM_MASK)
/*! @} */

/*! @name SEED - CRC seed register */
/*! @{ */
#define CRC_SEED_CRC_SEED_MASK                   (0xFFFFFFFFU)
#define CRC_SEED_CRC_SEED_SHIFT                  (0U)
#define CRC_SEED_CRC_SEED(x)                     (((uint32_t)(((uint32_t)(x)) << CRC_SEED_CRC_SEED_SHIFT)) & CRC_SEED_CRC_SEED_MASK)
/*! @} */

/*! @name SUM - CRC checksum register */
/*! @{ */
#define CRC_SUM_CRC_SUM_MASK                     (0xFFFFFFFFU)
#define CRC_SUM_CRC_SUM_SHIFT                    (0U)
#define CRC_SUM_CRC_SUM(x)                       (((uint32_t)(((uint32_t)(x)) << CRC_SUM_CRC_SUM_SHIFT)) & CRC_SUM_CRC_SUM_MASK)
/*! @} */

/*! @name WR_DATA - CRC data register */
/*! @{ */
#define CRC_WR_DATA_CRC_WR_DATA_MASK             (0xFFFFFFFFU)
#define CRC_WR_DATA_CRC_WR_DATA_SHIFT            (0U)
#define CRC_WR_DATA_CRC_WR_DATA(x)               (((uint32_t)(((uint32_t)(x)) << CRC_WR_DATA_CRC_WR_DATA_SHIFT)) & CRC_WR_DATA_CRC_WR_DATA_MASK)
/*! @} */


/*!
 * @}
 */ /* end of group CRC_Register_Masks */


/* CRC - Peripheral instance base addresses */
/** Peripheral CRC base address */
#define CRC_BASE                                 (0x50000000u)
/** Peripheral CRC base pointer */
#define CRC                                      ((CRC_Type *)CRC_BASE)
/** Array initializer of CRC peripheral base addresses */
#define CRC_BASE_ADDRS                           { CRC_BASE }
/** Array initializer of CRC peripheral base pointers */
#define CRC_BASE_PTRS                            { CRC }

/*!
 * @}
 */ /* end of group CRC_Peripheral_Access_Layer */


/* ----------------------------------------------------------------------------
   -- CTIMER Peripheral Access Layer
   ---------------------------------------------------------------------------- */

/*!
 * @addtogroup CTIMER_Peripheral_Access_Layer CTIMER Peripheral Access Layer
 * @{
 */

/** CTIMER - Register Layout Typedef */
typedef struct {
  __IO uint32_t IR;                                /**< Interrupt Register. The IR can be written to clear interrupts. The IR can be read to identify which of eight possible interrupt sources are pending., offset: 0x0 */
  __IO uint32_t TCR;                               /**< Timer Control Register. The TCR is used to control the Timer Counter functions. The Timer Counter can be disabled or reset through the TCR., offset: 0x4 */
  __IO uint32_t TC;                                /**< Timer Counter. The 32 bit TC is incremented every PR+1 cycles of the APB bus clock. The TC is controlled through the TCR., offset: 0x8 */
  __IO uint32_t PR;                                /**< Prescale Register. When the Prescale Counter (PC) is equal to this value, the next clock increments the TC and clears the PC., offset: 0xC */
  __IO uint32_t PC;                                /**< Prescale Counter. The 32 bit PC is a counter which is incremented to the value stored in PR. When the value in PR is reached, the TC is incremented and the PC is cleared. The PC is observable and controllable through the bus interface., offset: 0x10 */
  __IO uint32_t MCR;                               /**< Match Control Register. The MCR is used to control if an interrupt is generated and if the TC is reset when a Match occurs., offset: 0x14 */
  __IO uint32_t MR[4];                             /**< Match Register . MR can be enabled through the MCR to reset the TC, stop both the TC and PC, and/or generate an interrupt every time MR matches the TC., array offset: 0x18, array step: 0x4 */
  __IO uint32_t CCR;                               /**< Capture Control Register. The CCR controls which edges of the capture inputs are used to load the Capture Registers and whether or not an interrupt is generated when a capture takes place., offset: 0x28 */
  __I  uint32_t CR[3];                             /**< Capture Register . CR is loaded with the value of TC when there is an event on the CAPn. input., array offset: 0x2C, array step: 0x4 */
       uint8_t RESERVED_0[4];
  __IO uint32_t EMR;                               /**< External Match Register. The EMR controls the match function and the external match pins., offset: 0x3C */
       uint8_t RESERVED_1[48];
  __IO uint32_t CTCR;                              /**< Count Control Register. The CTCR selects between Timer and Counter mode, and in Counter mode selects the signal and edge(s) for counting., offset: 0x70 */
  __IO uint32_t PWMC;                              /**< PWM Control Register. The PWMCON enables PWM mode for the external match pins., offset: 0x74 */
  __IO uint32_t MSR[4];                            /**< Match Shadow Register . If enabled, the Match Register will be automatically reloaded with the contents of this register whenever the TC is reset to zero., array offset: 0x78, array step: 0x4 */
} CTIMER_Type;

/* ----------------------------------------------------------------------------
   -- CTIMER Register Masks
   ---------------------------------------------------------------------------- */

/*!
 * @addtogroup CTIMER_Register_Masks CTIMER Register Masks
 * @{
 */

/*! @name IR - Interrupt Register. The IR can be written to clear interrupts. The IR can be read to identify which of eight possible interrupt sources are pending. */
/*! @{ */
#define CTIMER_IR_MR0INT_MASK                    (0x1U)
#define CTIMER_IR_MR0INT_SHIFT                   (0U)
#define CTIMER_IR_MR0INT(x)                      (((uint32_t)(((uint32_t)(x)) << CTIMER_IR_MR0INT_SHIFT)) & CTIMER_IR_MR0INT_MASK)
#define CTIMER_IR_MR1INT_MASK                    (0x2U)
#define CTIMER_IR_MR1INT_SHIFT                   (1U)
#define CTIMER_IR_MR1INT(x)                      (((uint32_t)(((uint32_t)(x)) << CTIMER_IR_MR1INT_SHIFT)) & CTIMER_IR_MR1INT_MASK)
#define CTIMER_IR_MR2INT_MASK                    (0x4U)
#define CTIMER_IR_MR2INT_SHIFT                   (2U)
#define CTIMER_IR_MR2INT(x)                      (((uint32_t)(((uint32_t)(x)) << CTIMER_IR_MR2INT_SHIFT)) & CTIMER_IR_MR2INT_MASK)
#define CTIMER_IR_MR3INT_MASK                    (0x8U)
#define CTIMER_IR_MR3INT_SHIFT                   (3U)
#define CTIMER_IR_MR3INT(x)                      (((uint32_t)(((uint32_t)(x)) << CTIMER_IR_MR3INT_SHIFT)) & CTIMER_IR_MR3INT_MASK)
#define CTIMER_IR_CR0INT_MASK                    (0x10U)
#define CTIMER_IR_CR0INT_SHIFT                   (4U)
#define CTIMER_IR_CR0INT(x)                      (((uint32_t)(((uint32_t)(x)) << CTIMER_IR_CR0INT_SHIFT)) & CTIMER_IR_CR0INT_MASK)
#define CTIMER_IR_CR1INT_MASK                    (0x20U)
#define CTIMER_IR_CR1INT_SHIFT                   (5U)
#define CTIMER_IR_CR1INT(x)                      (((uint32_t)(((uint32_t)(x)) << CTIMER_IR_CR1INT_SHIFT)) & CTIMER_IR_CR1INT_MASK)
#define CTIMER_IR_CR2INT_MASK                    (0x40U)
#define CTIMER_IR_CR2INT_SHIFT                   (6U)
#define CTIMER_IR_CR2INT(x)                      (((uint32_t)(((uint32_t)(x)) << CTIMER_IR_CR2INT_SHIFT)) & CTIMER_IR_CR2INT_MASK)
/*! @} */

/*! @name TCR - Timer Control Register. The TCR is used to control the Timer Counter functions. The Timer Counter can be disabled or reset through the TCR. */
/*! @{ */
#define CTIMER_TCR_CEN_MASK                      (0x1U)
#define CTIMER_TCR_CEN_SHIFT                     (0U)
/*! CEN - Counter enable.
 *  0b0..Disabled.The counters are disabled.
 *  0b1..Enabled. The Timer Counter and Prescale Counter are enabled.
 */
#define CTIMER_TCR_CEN(x)                        (((uint32_t)(((uint32_t)(x)) << CTIMER_TCR_CEN_SHIFT)) & CTIMER_TCR_CEN_MASK)
#define CTIMER_TCR_CRST_MASK                     (0x2U)
#define CTIMER_TCR_CRST_SHIFT                    (1U)
/*! CRST - Counter reset.
 *  0b0..Disabled. Do nothing.
 *  0b1..Enabled. The Timer Counter and the Prescale Counter are synchronously reset on the next positive edge of
 *       the APB bus clock. The counters remain reset until TCR[1] is returned to zero.
 */
#define CTIMER_TCR_CRST(x)                       (((uint32_t)(((uint32_t)(x)) << CTIMER_TCR_CRST_SHIFT)) & CTIMER_TCR_CRST_MASK)
/*! @} */

/*! @name TC - Timer Counter. The 32 bit TC is incremented every PR+1 cycles of the APB bus clock. The TC is controlled through the TCR. */
/*! @{ */
#define CTIMER_TC_TCVAL_MASK                     (0xFFFFFFFFU)
#define CTIMER_TC_TCVAL_SHIFT                    (0U)
#define CTIMER_TC_TCVAL(x)                       (((uint32_t)(((uint32_t)(x)) << CTIMER_TC_TCVAL_SHIFT)) & CTIMER_TC_TCVAL_MASK)
/*! @} */

/*! @name PR - Prescale Register. When the Prescale Counter (PC) is equal to this value, the next clock increments the TC and clears the PC. */
/*! @{ */
#define CTIMER_PR_PRVAL_MASK                     (0xFFFFFFFFU)
#define CTIMER_PR_PRVAL_SHIFT                    (0U)
#define CTIMER_PR_PRVAL(x)                       (((uint32_t)(((uint32_t)(x)) << CTIMER_PR_PRVAL_SHIFT)) & CTIMER_PR_PRVAL_MASK)
/*! @} */

/*! @name PC - Prescale Counter. The 32 bit PC is a counter which is incremented to the value stored in PR. When the value in PR is reached, the TC is incremented and the PC is cleared. The PC is observable and controllable through the bus interface. */
/*! @{ */
#define CTIMER_PC_PCVAL_MASK                     (0xFFFFFFFFU)
#define CTIMER_PC_PCVAL_SHIFT                    (0U)
#define CTIMER_PC_PCVAL(x)                       (((uint32_t)(((uint32_t)(x)) << CTIMER_PC_PCVAL_SHIFT)) & CTIMER_PC_PCVAL_MASK)
/*! @} */

/*! @name MCR - Match Control Register. The MCR is used to control if an interrupt is generated and if the TC is reset when a Match occurs. */
/*! @{ */
#define CTIMER_MCR_MR0I_MASK                     (0x1U)
#define CTIMER_MCR_MR0I_SHIFT                    (0U)
#define CTIMER_MCR_MR0I(x)                       (((uint32_t)(((uint32_t)(x)) << CTIMER_MCR_MR0I_SHIFT)) & CTIMER_MCR_MR0I_MASK)
#define CTIMER_MCR_MR0R_MASK                     (0x2U)
#define CTIMER_MCR_MR0R_SHIFT                    (1U)
#define CTIMER_MCR_MR0R(x)                       (((uint32_t)(((uint32_t)(x)) << CTIMER_MCR_MR0R_SHIFT)) & CTIMER_MCR_MR0R_MASK)
#define CTIMER_MCR_MR0S_MASK                     (0x4U)
#define CTIMER_MCR_MR0S_SHIFT                    (2U)
#define CTIMER_MCR_MR0S(x)                       (((uint32_t)(((uint32_t)(x)) << CTIMER_MCR_MR0S_SHIFT)) & CTIMER_MCR_MR0S_MASK)
#define CTIMER_MCR_MR1I_MASK                     (0x8U)
#define CTIMER_MCR_MR1I_SHIFT                    (3U)
#define CTIMER_MCR_MR1I(x)                       (((uint32_t)(((uint32_t)(x)) << CTIMER_MCR_MR1I_SHIFT)) & CTIMER_MCR_MR1I_MASK)
#define CTIMER_MCR_MR1R_MASK                     (0x10U)
#define CTIMER_MCR_MR1R_SHIFT                    (4U)
#define CTIMER_MCR_MR1R(x)                       (((uint32_t)(((uint32_t)(x)) << CTIMER_MCR_MR1R_SHIFT)) & CTIMER_MCR_MR1R_MASK)
#define CTIMER_MCR_MR1S_MASK                     (0x20U)
#define CTIMER_MCR_MR1S_SHIFT                    (5U)
#define CTIMER_MCR_MR1S(x)                       (((uint32_t)(((uint32_t)(x)) << CTIMER_MCR_MR1S_SHIFT)) & CTIMER_MCR_MR1S_MASK)
#define CTIMER_MCR_MR2I_MASK                     (0x40U)
#define CTIMER_MCR_MR2I_SHIFT                    (6U)
#define CTIMER_MCR_MR2I(x)                       (((uint32_t)(((uint32_t)(x)) << CTIMER_MCR_MR2I_SHIFT)) & CTIMER_MCR_MR2I_MASK)
#define CTIMER_MCR_MR2R_MASK                     (0x80U)
#define CTIMER_MCR_MR2R_SHIFT                    (7U)
#define CTIMER_MCR_MR2R(x)                       (((uint32_t)(((uint32_t)(x)) << CTIMER_MCR_MR2R_SHIFT)) & CTIMER_MCR_MR2R_MASK)
#define CTIMER_MCR_MR2S_MASK                     (0x100U)
#define CTIMER_MCR_MR2S_SHIFT                    (8U)
#define CTIMER_MCR_MR2S(x)                       (((uint32_t)(((uint32_t)(x)) << CTIMER_MCR_MR2S_SHIFT)) & CTIMER_MCR_MR2S_MASK)
#define CTIMER_MCR_MR3I_MASK                     (0x200U)
#define CTIMER_MCR_MR3I_SHIFT                    (9U)
#define CTIMER_MCR_MR3I(x)                       (((uint32_t)(((uint32_t)(x)) << CTIMER_MCR_MR3I_SHIFT)) & CTIMER_MCR_MR3I_MASK)
#define CTIMER_MCR_MR3R_MASK                     (0x400U)
#define CTIMER_MCR_MR3R_SHIFT                    (10U)
#define CTIMER_MCR_MR3R(x)                       (((uint32_t)(((uint32_t)(x)) << CTIMER_MCR_MR3R_SHIFT)) & CTIMER_MCR_MR3R_MASK)
#define CTIMER_MCR_MR3S_MASK                     (0x800U)
#define CTIMER_MCR_MR3S_SHIFT                    (11U)
#define CTIMER_MCR_MR3S(x)                       (((uint32_t)(((uint32_t)(x)) << CTIMER_MCR_MR3S_SHIFT)) & CTIMER_MCR_MR3S_MASK)
#define CTIMER_MCR_MR0RL_MASK                    (0x1000000U)
#define CTIMER_MCR_MR0RL_SHIFT                   (24U)
#define CTIMER_MCR_MR0RL(x)                      (((uint32_t)(((uint32_t)(x)) << CTIMER_MCR_MR0RL_SHIFT)) & CTIMER_MCR_MR0RL_MASK)
#define CTIMER_MCR_MR1RL_MASK                    (0x2000000U)
#define CTIMER_MCR_MR1RL_SHIFT                   (25U)
#define CTIMER_MCR_MR1RL(x)                      (((uint32_t)(((uint32_t)(x)) << CTIMER_MCR_MR1RL_SHIFT)) & CTIMER_MCR_MR1RL_MASK)
#define CTIMER_MCR_MR2RL_MASK                    (0x4000000U)
#define CTIMER_MCR_MR2RL_SHIFT                   (26U)
#define CTIMER_MCR_MR2RL(x)                      (((uint32_t)(((uint32_t)(x)) << CTIMER_MCR_MR2RL_SHIFT)) & CTIMER_MCR_MR2RL_MASK)
#define CTIMER_MCR_MR3RL_MASK                    (0x8000000U)
#define CTIMER_MCR_MR3RL_SHIFT                   (27U)
#define CTIMER_MCR_MR3RL(x)                      (((uint32_t)(((uint32_t)(x)) << CTIMER_MCR_MR3RL_SHIFT)) & CTIMER_MCR_MR3RL_MASK)
/*! @} */

/*! @name MR - Match Register . MR can be enabled through the MCR to reset the TC, stop both the TC and PC, and/or generate an interrupt every time MR matches the TC. */
/*! @{ */
#define CTIMER_MR_MATCH_MASK                     (0xFFFFFFFFU)
#define CTIMER_MR_MATCH_SHIFT                    (0U)
#define CTIMER_MR_MATCH(x)                       (((uint32_t)(((uint32_t)(x)) << CTIMER_MR_MATCH_SHIFT)) & CTIMER_MR_MATCH_MASK)
/*! @} */

/* The count of CTIMER_MR */
#define CTIMER_MR_COUNT                          (4U)

/*! @name CCR - Capture Control Register. The CCR controls which edges of the capture inputs are used to load the Capture Registers and whether or not an interrupt is generated when a capture takes place. */
/*! @{ */
#define CTIMER_CCR_CAP0RE_MASK                   (0x1U)
#define CTIMER_CCR_CAP0RE_SHIFT                  (0U)
#define CTIMER_CCR_CAP0RE(x)                     (((uint32_t)(((uint32_t)(x)) << CTIMER_CCR_CAP0RE_SHIFT)) & CTIMER_CCR_CAP0RE_MASK)
#define CTIMER_CCR_CAP0FE_MASK                   (0x2U)
#define CTIMER_CCR_CAP0FE_SHIFT                  (1U)
#define CTIMER_CCR_CAP0FE(x)                     (((uint32_t)(((uint32_t)(x)) << CTIMER_CCR_CAP0FE_SHIFT)) & CTIMER_CCR_CAP0FE_MASK)
#define CTIMER_CCR_CAP0I_MASK                    (0x4U)
#define CTIMER_CCR_CAP0I_SHIFT                   (2U)
#define CTIMER_CCR_CAP0I(x)                      (((uint32_t)(((uint32_t)(x)) << CTIMER_CCR_CAP0I_SHIFT)) & CTIMER_CCR_CAP0I_MASK)
#define CTIMER_CCR_CAP1RE_MASK                   (0x8U)
#define CTIMER_CCR_CAP1RE_SHIFT                  (3U)
#define CTIMER_CCR_CAP1RE(x)                     (((uint32_t)(((uint32_t)(x)) << CTIMER_CCR_CAP1RE_SHIFT)) & CTIMER_CCR_CAP1RE_MASK)
#define CTIMER_CCR_CAP1FE_MASK                   (0x10U)
#define CTIMER_CCR_CAP1FE_SHIFT                  (4U)
#define CTIMER_CCR_CAP1FE(x)                     (((uint32_t)(((uint32_t)(x)) << CTIMER_CCR_CAP1FE_SHIFT)) & CTIMER_CCR_CAP1FE_MASK)
#define CTIMER_CCR_CAP1I_MASK                    (0x20U)
#define CTIMER_CCR_CAP1I_SHIFT                   (5U)
#define CTIMER_CCR_CAP1I(x)                      (((uint32_t)(((uint32_t)(x)) << CTIMER_CCR_CAP1I_SHIFT)) & CTIMER_CCR_CAP1I_MASK)
#define CTIMER_CCR_CAP2RE_MASK                   (0x40U)
#define CTIMER_CCR_CAP2RE_SHIFT                  (6U)
#define CTIMER_CCR_CAP2RE(x)                     (((uint32_t)(((uint32_t)(x)) << CTIMER_CCR_CAP2RE_SHIFT)) & CTIMER_CCR_CAP2RE_MASK)
#define CTIMER_CCR_CAP2FE_MASK                   (0x80U)
#define CTIMER_CCR_CAP2FE_SHIFT                  (7U)
#define CTIMER_CCR_CAP2FE(x)                     (((uint32_t)(((uint32_t)(x)) << CTIMER_CCR_CAP2FE_SHIFT)) & CTIMER_CCR_CAP2FE_MASK)
#define CTIMER_CCR_CAP2I_MASK                    (0x100U)
#define CTIMER_CCR_CAP2I_SHIFT                   (8U)
#define CTIMER_CCR_CAP2I(x)                      (((uint32_t)(((uint32_t)(x)) << CTIMER_CCR_CAP2I_SHIFT)) & CTIMER_CCR_CAP2I_MASK)
/*! @} */

/*! @name CR - Capture Register . CR is loaded with the value of TC when there is an event on the CAPn. input. */
/*! @{ */
#define CTIMER_CR_CAP_MASK                       (0xFFFFFFFFU)
#define CTIMER_CR_CAP_SHIFT                      (0U)
#define CTIMER_CR_CAP(x)                         (((uint32_t)(((uint32_t)(x)) << CTIMER_CR_CAP_SHIFT)) & CTIMER_CR_CAP_MASK)
/*! @} */

/* The count of CTIMER_CR */
#define CTIMER_CR_COUNT                          (3U)

/*! @name EMR - External Match Register. The EMR controls the match function and the external match pins. */
/*! @{ */
#define CTIMER_EMR_EM0_MASK                      (0x1U)
#define CTIMER_EMR_EM0_SHIFT                     (0U)
#define CTIMER_EMR_EM0(x)                        (((uint32_t)(((uint32_t)(x)) << CTIMER_EMR_EM0_SHIFT)) & CTIMER_EMR_EM0_MASK)
#define CTIMER_EMR_EM1_MASK                      (0x2U)
#define CTIMER_EMR_EM1_SHIFT                     (1U)
#define CTIMER_EMR_EM1(x)                        (((uint32_t)(((uint32_t)(x)) << CTIMER_EMR_EM1_SHIFT)) & CTIMER_EMR_EM1_MASK)
#define CTIMER_EMR_EM2_MASK                      (0x4U)
#define CTIMER_EMR_EM2_SHIFT                     (2U)
#define CTIMER_EMR_EM2(x)                        (((uint32_t)(((uint32_t)(x)) << CTIMER_EMR_EM2_SHIFT)) & CTIMER_EMR_EM2_MASK)
#define CTIMER_EMR_EM3_MASK                      (0x8U)
#define CTIMER_EMR_EM3_SHIFT                     (3U)
#define CTIMER_EMR_EM3(x)                        (((uint32_t)(((uint32_t)(x)) << CTIMER_EMR_EM3_SHIFT)) & CTIMER_EMR_EM3_MASK)
#define CTIMER_EMR_EMC0_MASK                     (0x30U)
#define CTIMER_EMR_EMC0_SHIFT                    (4U)
/*! EMC0 - External Match Control 0. Determines the functionality of External Match 0.
 *  0b00..Do Nothing.
 *  0b01..Clear. Clear the corresponding External Match bit/output to 0 (MAT0 pin is LOW if pinned out).
 *  0b10..Set. Set the corresponding External Match bit/output to 1 (MAT0 pin is HIGH if pinned out).
 *  0b11..Toggle. Toggle the corresponding External Match bit/output.
 */
#define CTIMER_EMR_EMC0(x)                       (((uint32_t)(((uint32_t)(x)) << CTIMER_EMR_EMC0_SHIFT)) & CTIMER_EMR_EMC0_MASK)
#define CTIMER_EMR_EMC1_MASK                     (0xC0U)
#define CTIMER_EMR_EMC1_SHIFT                    (6U)
/*! EMC1 - External Match Control 1. Determines the functionality of External Match 1.
 *  0b00..Do Nothing.
 *  0b01..Clear. Clear the corresponding External Match bit/output to 0 (MAT1 pin is LOW if pinned out).
 *  0b10..Set. Set the corresponding External Match bit/output to 1 (MAT1 pin is HIGH if pinned out).
 *  0b11..Toggle. Toggle the corresponding External Match bit/output.
 */
#define CTIMER_EMR_EMC1(x)                       (((uint32_t)(((uint32_t)(x)) << CTIMER_EMR_EMC1_SHIFT)) & CTIMER_EMR_EMC1_MASK)
#define CTIMER_EMR_EMC2_MASK                     (0x300U)
#define CTIMER_EMR_EMC2_SHIFT                    (8U)
/*! EMC2 - External Match Control 2. Determines the functionality of External Match 2.
 *  0b00..Do Nothing.
 *  0b01..Clear. Clear the corresponding External Match bit/output to 0 (MAT2 pin is LOW if pinned out).
 *  0b10..Set. Set the corresponding External Match bit/output to 1 (MAT2 pin is HIGH if pinned out).
 *  0b11..Toggle. Toggle the corresponding External Match bit/output.
 */
#define CTIMER_EMR_EMC2(x)                       (((uint32_t)(((uint32_t)(x)) << CTIMER_EMR_EMC2_SHIFT)) & CTIMER_EMR_EMC2_MASK)
#define CTIMER_EMR_EMC3_MASK                     (0xC00U)
#define CTIMER_EMR_EMC3_SHIFT                    (10U)
/*! EMC3 - External Match Control 3. Determines the functionality of External Match 3.
 *  0b00..Do Nothing.
 *  0b01..Clear. Clear the corresponding External Match bit/output to 0 (MAT3 pin is LOW if pinned out).
 *  0b10..Set. Set the corresponding External Match bit/output to 1 (MAT3 pin is HIGH if pinned out).
 *  0b11..Toggle. Toggle the corresponding External Match bit/output.
 */
#define CTIMER_EMR_EMC3(x)                       (((uint32_t)(((uint32_t)(x)) << CTIMER_EMR_EMC3_SHIFT)) & CTIMER_EMR_EMC3_MASK)
/*! @} */

/*! @name CTCR - Count Control Register. The CTCR selects between Timer and Counter mode, and in Counter mode selects the signal and edge(s) for counting. */
/*! @{ */
#define CTIMER_CTCR_CTMODE_MASK                  (0x3U)
#define CTIMER_CTCR_CTMODE_SHIFT                 (0U)
/*! CTMODE - Counter/Timer Mode This field selects which rising APB bus clock edges can increment
 *    Timer's Prescale Counter (PC), or clear PC and increment Timer Counter (TC). Timer Mode: the TC
 *    is incremented when the Prescale Counter matches the Prescale Register.
 *  0b00..Timer Mode. Incremented every rising APB bus clock edge.
 *  0b01..Counter Mode rising edge. TC is incremented on rising edges on the CAP input selected by bits 3:2.
 *  0b10..Counter Mode falling edge. TC is incremented on falling edges on the CAP input selected by bits 3:2.
 *  0b11..Counter Mode dual edge. TC is incremented on both edges on the CAP input selected by bits 3:2.
 */
#define CTIMER_CTCR_CTMODE(x)                    (((uint32_t)(((uint32_t)(x)) << CTIMER_CTCR_CTMODE_SHIFT)) & CTIMER_CTCR_CTMODE_MASK)
#define CTIMER_CTCR_CINSEL_MASK                  (0xCU)
#define CTIMER_CTCR_CINSEL_SHIFT                 (2U)
/*! CINSEL - Count Input Select When bits 1:0 in this register are not 00, these bits select which
 *    CAP pin is sampled for clocking. Note: If Counter mode is selected for a particular CAPn input
 *    in the CTCR, the 3 bits for that input in the Capture Control Register (CCR) must be
 *    programmed as 000. However, capture and/or interrupt can be selected for the other 3 CAPn inputs in the
 *    same timer.
 *  0b00..Channel 0. CAPn.0 for CTIMERn
 *  0b01..Channel 1. CAPn.1 for CTIMERn
 *  0b10..Channel 2. CAPn.2 for CTIMERn
 *  0b11..Channel 3. CAPn.3 for CTIMERn
 */
#define CTIMER_CTCR_CINSEL(x)                    (((uint32_t)(((uint32_t)(x)) << CTIMER_CTCR_CINSEL_SHIFT)) & CTIMER_CTCR_CINSEL_MASK)
#define CTIMER_CTCR_ENCC_MASK                    (0x10U)
#define CTIMER_CTCR_ENCC_SHIFT                   (4U)
#define CTIMER_CTCR_ENCC(x)                      (((uint32_t)(((uint32_t)(x)) << CTIMER_CTCR_ENCC_SHIFT)) & CTIMER_CTCR_ENCC_MASK)
#define CTIMER_CTCR_SELCC_MASK                   (0xE0U)
#define CTIMER_CTCR_SELCC_SHIFT                  (5U)
/*! SELCC - Edge select. When bit 4 is 1, these bits select which capture input edge will cause the
 *    timer and prescaler to be cleared. These bits have no effect when bit 4 is low. Values 0x2 to
 *    0x3 and 0x6 to 0x7 are reserved.
 *  0b000..Channel 0 Rising Edge. Rising edge of the signal on capture channel 0 clears the timer (if bit 4 is set).
 *  0b001..Channel 0 Falling Edge. Falling edge of the signal on capture channel 0 clears the timer (if bit 4 is set).
 *  0b010..Channel 1 Rising Edge. Rising edge of the signal on capture channel 1 clears the timer (if bit 4 is set).
 *  0b011..Channel 1 Falling Edge. Falling edge of the signal on capture channel 1 clears the timer (if bit 4 is set).
 *  0b100..Channel 2 Rising Edge. Rising edge of the signal on capture channel 2 clears the timer (if bit 4 is set).
 *  0b101..Channel 2 Falling Edge. Falling edge of the signal on capture channel 2 clears the timer (if bit 4 is set).
 */
#define CTIMER_CTCR_SELCC(x)                     (((uint32_t)(((uint32_t)(x)) << CTIMER_CTCR_SELCC_SHIFT)) & CTIMER_CTCR_SELCC_MASK)
/*! @} */

/*! @name PWMC - PWM Control Register. The PWMCON enables PWM mode for the external match pins. */
/*! @{ */
#define CTIMER_PWMC_PWMEN0_MASK                  (0x1U)
#define CTIMER_PWMC_PWMEN0_SHIFT                 (0U)
/*! PWMEN0 - PWM mode enable for channel0.
 *  0b0..Match. CTIMERn_MAT0 is controlled by EM0.
 *  0b1..PWM. PWM mode is enabled for CTIMERn_MAT0.
 */
#define CTIMER_PWMC_PWMEN0(x)                    (((uint32_t)(((uint32_t)(x)) << CTIMER_PWMC_PWMEN0_SHIFT)) & CTIMER_PWMC_PWMEN0_MASK)
#define CTIMER_PWMC_PWMEN1_MASK                  (0x2U)
#define CTIMER_PWMC_PWMEN1_SHIFT                 (1U)
/*! PWMEN1 - PWM mode enable for channel1.
 *  0b0..Match. CTIMERn_MAT01 is controlled by EM1.
 *  0b1..PWM. PWM mode is enabled for CTIMERn_MAT1.
 */
#define CTIMER_PWMC_PWMEN1(x)                    (((uint32_t)(((uint32_t)(x)) << CTIMER_PWMC_PWMEN1_SHIFT)) & CTIMER_PWMC_PWMEN1_MASK)
#define CTIMER_PWMC_PWMEN2_MASK                  (0x4U)
#define CTIMER_PWMC_PWMEN2_SHIFT                 (2U)
/*! PWMEN2 - PWM mode enable for channel2.
 *  0b0..Match. CTIMERn_MAT2 is controlled by EM2.
 *  0b1..PWM. PWM mode is enabled for CTIMERn_MAT2.
 */
#define CTIMER_PWMC_PWMEN2(x)                    (((uint32_t)(((uint32_t)(x)) << CTIMER_PWMC_PWMEN2_SHIFT)) & CTIMER_PWMC_PWMEN2_MASK)
#define CTIMER_PWMC_PWMEN3_MASK                  (0x8U)
#define CTIMER_PWMC_PWMEN3_SHIFT                 (3U)
/*! PWMEN3 - PWM mode enable for channel3. Note: It is recommended to use match channel 3 to set the PWM cycle.
 *  0b0..Match. CTIMERn_MAT3 is controlled by EM3.
 *  0b1..PWM. PWM mode is enabled for CT132Bn_MAT3.
 */
#define CTIMER_PWMC_PWMEN3(x)                    (((uint32_t)(((uint32_t)(x)) << CTIMER_PWMC_PWMEN3_SHIFT)) & CTIMER_PWMC_PWMEN3_MASK)
/*! @} */

/*! @name MSR - Match Shadow Register . If enabled, the Match Register will be automatically reloaded with the contents of this register whenever the TC is reset to zero. */
/*! @{ */
#define CTIMER_MSR_MATCH_Shadow_MASK             (0xFFFFFFFFU)
#define CTIMER_MSR_MATCH_Shadow_SHIFT            (0U)
#define CTIMER_MSR_MATCH_Shadow(x)               (((uint32_t)(((uint32_t)(x)) << CTIMER_MSR_MATCH_Shadow_SHIFT)) & CTIMER_MSR_MATCH_Shadow_MASK)
/*! @} */

/* The count of CTIMER_MSR */
#define CTIMER_MSR_COUNT                         (4U)


/*!
 * @}
 */ /* end of group CTIMER_Register_Masks */


/* CTIMER - Peripheral instance base addresses */
/** Peripheral CTIMER0 base address */
#define CTIMER0_BASE                             (0x40038000u)
/** Peripheral CTIMER0 base pointer */
#define CTIMER0                                  ((CTIMER_Type *)CTIMER0_BASE)
/** Array initializer of CTIMER peripheral base addresses */
#define CTIMER_BASE_ADDRS                        { CTIMER0_BASE }
/** Array initializer of CTIMER peripheral base pointers */
#define CTIMER_BASE_PTRS                         { CTIMER0 }
/** Interrupt vectors for the CTIMER peripheral type */
#define CTIMER_IRQS                              { CTIMER0_IRQn }

/*!
 * @}
 */ /* end of group CTIMER_Peripheral_Access_Layer */


/* ----------------------------------------------------------------------------
   -- DAC Peripheral Access Layer
   ---------------------------------------------------------------------------- */

/*!
 * @addtogroup DAC_Peripheral_Access_Layer DAC Peripheral Access Layer
 * @{
 */

/** DAC - Register Layout Typedef */
typedef struct {
  __IO uint32_t CR;                                /**< D/A Converter Register. This register contains the digital value to be converted to analog and a power control bit., offset: 0x0 */
  __IO uint32_t CTRL;                              /**< DAC Control register. This register controls DMA and timer operation., offset: 0x4 */
  __IO uint32_t CNTVAL;                            /**< DAC Counter Value register. This register contains the reload value for the DAC DMA/Interrupt timer., offset: 0x8 */
} DAC_Type;

/* ----------------------------------------------------------------------------
   -- DAC Register Masks
   ---------------------------------------------------------------------------- */

/*!
 * @addtogroup DAC_Register_Masks DAC Register Masks
 * @{
 */

/*! @name CR - D/A Converter Register. This register contains the digital value to be converted to analog and a power control bit. */
/*! @{ */
#define DAC_CR_VALUE_MASK                        (0xFFC0U)
#define DAC_CR_VALUE_SHIFT                       (6U)
#define DAC_CR_VALUE(x)                          (((uint32_t)(((uint32_t)(x)) << DAC_CR_VALUE_SHIFT)) & DAC_CR_VALUE_MASK)
#define DAC_CR_BIAS_MASK                         (0x10000U)
#define DAC_CR_BIAS_SHIFT                        (16U)
/*! BIAS - The settling time of the DAC
 *  0b0..The settling time of the DAC is 1 us max, and the maximum current is 700 uA. This allows a maximum update rate of 1 MHz.
 *  0b1..The settling time of the DAC is 2.5 us and the maximum current is 350 uA. This allows a maximum update rate of 400 kHz.
 */
#define DAC_CR_BIAS(x)                           (((uint32_t)(((uint32_t)(x)) << DAC_CR_BIAS_SHIFT)) & DAC_CR_BIAS_MASK)
/*! @} */

/*! @name CTRL - DAC Control register. This register controls DMA and timer operation. */
/*! @{ */
#define DAC_CTRL_INT_CPU_REQ_MASK                (0x1U)
#define DAC_CTRL_INT_CPU_REQ_SHIFT               (0U)
/*! INT_CPU_REQ - Interrupt request to CPU. This interrupt request is handled by the CPU.
 *  0b0..Clear on any write to the CR register.
 *  0b1..Set by hardware when the timer times out.
 */
#define DAC_CTRL_INT_CPU_REQ(x)                  (((uint32_t)(((uint32_t)(x)) << DAC_CTRL_INT_CPU_REQ_SHIFT)) & DAC_CTRL_INT_CPU_REQ_MASK)
#define DAC_CTRL_DBLBUF_ENA_MASK                 (0x2U)
#define DAC_CTRL_DBLBUF_ENA_SHIFT                (1U)
/*! DBLBUF_ENA - dacr double buffer
 *  0b0..DACR double-buffering is disabled.
 *  0b1..When this bit and the CNT_ENA bit are both set, the double-buffering feature in the DACR register will be
 *       enabled. Writes to the DACR register are written to a pre-buffer and then transferred to the DACR on the
 *       next time-out of the counter.
 */
#define DAC_CTRL_DBLBUF_ENA(x)                   (((uint32_t)(((uint32_t)(x)) << DAC_CTRL_DBLBUF_ENA_SHIFT)) & DAC_CTRL_DBLBUF_ENA_MASK)
#define DAC_CTRL_CNT_ENA_MASK                    (0x4U)
#define DAC_CTRL_CNT_ENA_SHIFT                   (2U)
/*! CNT_ENA - time-out counter operation
 *  0b0..Time-out counter operation is disabled.
 *  0b1..Time-out counter operation is enabled.
 */
#define DAC_CTRL_CNT_ENA(x)                      (((uint32_t)(((uint32_t)(x)) << DAC_CTRL_CNT_ENA_SHIFT)) & DAC_CTRL_CNT_ENA_MASK)
/*! @} */

/*! @name CNTVAL - DAC Counter Value register. This register contains the reload value for the DAC DMA/Interrupt timer. */
/*! @{ */
#define DAC_CNTVAL_VALUE_MASK                    (0xFFFFU)
#define DAC_CNTVAL_VALUE_SHIFT                   (0U)
#define DAC_CNTVAL_VALUE(x)                      (((uint32_t)(((uint32_t)(x)) << DAC_CNTVAL_VALUE_SHIFT)) & DAC_CNTVAL_VALUE_MASK)
/*! @} */


/*!
 * @}
 */ /* end of group DAC_Register_Masks */


/* DAC - Peripheral instance base addresses */
/** Peripheral DAC0 base address */
#define DAC0_BASE                                (0x40014000u)
/** Peripheral DAC0 base pointer */
#define DAC0                                     ((DAC_Type *)DAC0_BASE)
/** Array initializer of DAC peripheral base addresses */
#define DAC_BASE_ADDRS                           { DAC0_BASE }
/** Array initializer of DAC peripheral base pointers */
#define DAC_BASE_PTRS                            { DAC0 }

/*!
 * @}
 */ /* end of group DAC_Peripheral_Access_Layer */


/* ----------------------------------------------------------------------------
   -- GPIO Peripheral Access Layer
   ---------------------------------------------------------------------------- */

/*!
 * @addtogroup GPIO_Peripheral_Access_Layer GPIO Peripheral Access Layer
 * @{
 */

/** GPIO - Register Layout Typedef */
typedef struct {
  __IO uint8_t B[1][31];                           /**< Byte pin registers for all port 0 and 1 GPIO pins, array offset: 0x0, array step: index*0x1F, index2*0x1 */
       uint8_t RESERVED_0[4065];
  __IO uint32_t W[1][31];                          /**< Word pin registers for all port 0 and 1 GPIO pins, array offset: 0x1000, array step: index*0x7C, index2*0x4 */
       uint8_t RESERVED_1[3972];
  __IO uint32_t DIR[1];                            /**< Direction registers, array offset: 0x2000, array step: 0x4 */
       uint8_t RESERVED_2[124];
  __IO uint32_t MASK[1];                           /**< Mask register, array offset: 0x2080, array step: 0x4 */
       uint8_t RESERVED_3[124];
  __IO uint32_t PIN[1];                            /**< Port pin register, array offset: 0x2100, array step: 0x4 */
       uint8_t RESERVED_4[124];
  __IO uint32_t MPIN[1];                           /**< Masked port register, array offset: 0x2180, array step: 0x4 */
       uint8_t RESERVED_5[124];
  __IO uint32_t SET[1];                            /**< Write: Set register for port Read: output bits for port, array offset: 0x2200, array step: 0x4 */
       uint8_t RESERVED_6[124];
  __O  uint32_t CLR[1];                            /**< Clear port, array offset: 0x2280, array step: 0x4 */
       uint8_t RESERVED_7[124];
  __O  uint32_t NOT[1];                            /**< Toggle port, array offset: 0x2300, array step: 0x4 */
       uint8_t RESERVED_8[124];
  __O  uint32_t DIRSET[1];                         /**< Set pin direction bits for port, array offset: 0x2380, array step: 0x4 */
       uint8_t RESERVED_9[124];
  __O  uint32_t DIRCLR[1];                         /**< Clear pin direction bits for port, array offset: 0x2400, array step: 0x4 */
       uint8_t RESERVED_10[124];
  __O  uint32_t DIRNOT[1];                         /**< Toggle pin direction bits for port, array offset: 0x2480, array step: 0x4 */
} GPIO_Type;

/* ----------------------------------------------------------------------------
   -- GPIO Register Masks
   ---------------------------------------------------------------------------- */

/*!
 * @addtogroup GPIO_Register_Masks GPIO Register Masks
 * @{
 */

/*! @name B - Byte pin registers for all port 0 and 1 GPIO pins */
/*! @{ */
#define GPIO_B_PBYTE_MASK                        (0x1U)
#define GPIO_B_PBYTE_SHIFT                       (0U)
#define GPIO_B_PBYTE(x)                          (((uint8_t)(((uint8_t)(x)) << GPIO_B_PBYTE_SHIFT)) & GPIO_B_PBYTE_MASK)
/*! @} */

/* The count of GPIO_B */
#define GPIO_B_COUNT                             (1U)

/* The count of GPIO_B */
#define GPIO_B_COUNT2                            (31U)

/*! @name W - Word pin registers for all port 0 and 1 GPIO pins */
/*! @{ */
#define GPIO_W_PWORD_MASK                        (0xFFFFFFFFU)
#define GPIO_W_PWORD_SHIFT                       (0U)
#define GPIO_W_PWORD(x)                          (((uint32_t)(((uint32_t)(x)) << GPIO_W_PWORD_SHIFT)) & GPIO_W_PWORD_MASK)
/*! @} */

/* The count of GPIO_W */
#define GPIO_W_COUNT                             (1U)

/* The count of GPIO_W */
#define GPIO_W_COUNT2                            (31U)

/*! @name DIR - Direction registers */
/*! @{ */
#define GPIO_DIR_DIRP_MASK                       (0x7FFFFFFFU)
#define GPIO_DIR_DIRP_SHIFT                      (0U)
#define GPIO_DIR_DIRP(x)                         (((uint32_t)(((uint32_t)(x)) << GPIO_DIR_DIRP_SHIFT)) & GPIO_DIR_DIRP_MASK)
/*! @} */

/* The count of GPIO_DIR */
#define GPIO_DIR_COUNT                           (1U)

/*! @name MASK - Mask register */
/*! @{ */
#define GPIO_MASK_MASKP_MASK                     (0x7FFFFFFFU)
#define GPIO_MASK_MASKP_SHIFT                    (0U)
#define GPIO_MASK_MASKP(x)                       (((uint32_t)(((uint32_t)(x)) << GPIO_MASK_MASKP_SHIFT)) & GPIO_MASK_MASKP_MASK)
/*! @} */

/* The count of GPIO_MASK */
#define GPIO_MASK_COUNT                          (1U)

/*! @name PIN - Port pin register */
/*! @{ */
#define GPIO_PIN_PORT_MASK                       (0x7FFFFFFFU)
#define GPIO_PIN_PORT_SHIFT                      (0U)
#define GPIO_PIN_PORT(x)                         (((uint32_t)(((uint32_t)(x)) << GPIO_PIN_PORT_SHIFT)) & GPIO_PIN_PORT_MASK)
/*! @} */

/* The count of GPIO_PIN */
#define GPIO_PIN_COUNT                           (1U)

/*! @name MPIN - Masked port register */
/*! @{ */
#define GPIO_MPIN_MPORTP_MASK                    (0x7FFFFFFFU)
#define GPIO_MPIN_MPORTP_SHIFT                   (0U)
#define GPIO_MPIN_MPORTP(x)                      (((uint32_t)(((uint32_t)(x)) << GPIO_MPIN_MPORTP_SHIFT)) & GPIO_MPIN_MPORTP_MASK)
/*! @} */

/* The count of GPIO_MPIN */
#define GPIO_MPIN_COUNT                          (1U)

/*! @name SET - Write: Set register for port Read: output bits for port */
/*! @{ */
#define GPIO_SET_SETP_MASK                       (0x7FFFFFFFU)
#define GPIO_SET_SETP_SHIFT                      (0U)
#define GPIO_SET_SETP(x)                         (((uint32_t)(((uint32_t)(x)) << GPIO_SET_SETP_SHIFT)) & GPIO_SET_SETP_MASK)
/*! @} */

/* The count of GPIO_SET */
#define GPIO_SET_COUNT                           (1U)

/*! @name CLR - Clear port */
/*! @{ */
#define GPIO_CLR_CLRP_MASK                       (0x7FFFFFFFU)
#define GPIO_CLR_CLRP_SHIFT                      (0U)
#define GPIO_CLR_CLRP(x)                         (((uint32_t)(((uint32_t)(x)) << GPIO_CLR_CLRP_SHIFT)) & GPIO_CLR_CLRP_MASK)
/*! @} */

/* The count of GPIO_CLR */
#define GPIO_CLR_COUNT                           (1U)

/*! @name NOT - Toggle port */
/*! @{ */
#define GPIO_NOT_NOTP_MASK                       (0x7FFFFFFFU)
#define GPIO_NOT_NOTP_SHIFT                      (0U)
#define GPIO_NOT_NOTP(x)                         (((uint32_t)(((uint32_t)(x)) << GPIO_NOT_NOTP_SHIFT)) & GPIO_NOT_NOTP_MASK)
/*! @} */

/* The count of GPIO_NOT */
#define GPIO_NOT_COUNT                           (1U)

/*! @name DIRSET - Set pin direction bits for port */
/*! @{ */
#define GPIO_DIRSET_DIRSETP_MASK                 (0x7FFFFFFFU)
#define GPIO_DIRSET_DIRSETP_SHIFT                (0U)
#define GPIO_DIRSET_DIRSETP(x)                   (((uint32_t)(((uint32_t)(x)) << GPIO_DIRSET_DIRSETP_SHIFT)) & GPIO_DIRSET_DIRSETP_MASK)
/*! @} */

/* The count of GPIO_DIRSET */
#define GPIO_DIRSET_COUNT                        (1U)

/*! @name DIRCLR - Clear pin direction bits for port */
/*! @{ */
#define GPIO_DIRCLR_DIRCLRP_MASK                 (0x7FFFFFFFU)
#define GPIO_DIRCLR_DIRCLRP_SHIFT                (0U)
#define GPIO_DIRCLR_DIRCLRP(x)                   (((uint32_t)(((uint32_t)(x)) << GPIO_DIRCLR_DIRCLRP_SHIFT)) & GPIO_DIRCLR_DIRCLRP_MASK)
/*! @} */

/* The count of GPIO_DIRCLR */
#define GPIO_DIRCLR_COUNT                        (1U)

/*! @name DIRNOT - Toggle pin direction bits for port */
/*! @{ */
#define GPIO_DIRNOT_DIRNOTP_MASK                 (0x7FFFFFFFU)
#define GPIO_DIRNOT_DIRNOTP_SHIFT                (0U)
#define GPIO_DIRNOT_DIRNOTP(x)                   (((uint32_t)(((uint32_t)(x)) << GPIO_DIRNOT_DIRNOTP_SHIFT)) & GPIO_DIRNOT_DIRNOTP_MASK)
/*! @} */

/* The count of GPIO_DIRNOT */
#define GPIO_DIRNOT_COUNT                        (1U)


/*!
 * @}
 */ /* end of group GPIO_Register_Masks */


/* GPIO - Peripheral instance base addresses */
/** Peripheral GPIO base address */
#define GPIO_BASE                                (0xA0000000u)
/** Peripheral GPIO base pointer */
#define GPIO                                     ((GPIO_Type *)GPIO_BASE)
/** Array initializer of GPIO peripheral base addresses */
#define GPIO_BASE_ADDRS                          { GPIO_BASE }
/** Array initializer of GPIO peripheral base pointers */
#define GPIO_BASE_PTRS                           { GPIO }

/*!
 * @}
 */ /* end of group GPIO_Peripheral_Access_Layer */


/* ----------------------------------------------------------------------------
   -- I2C Peripheral Access Layer
   ---------------------------------------------------------------------------- */

/*!
 * @addtogroup I2C_Peripheral_Access_Layer I2C Peripheral Access Layer
 * @{
 */

/** I2C - Register Layout Typedef */
typedef struct {
  __IO uint32_t CFG;                               /**< Configuration for shared functions., offset: 0x0 */
  __IO uint32_t STAT;                              /**< Status register for Master, Slave, and Monitor functions., offset: 0x4 */
  __IO uint32_t INTENSET;                          /**< Interrupt Enable Set and read register., offset: 0x8 */
  __O  uint32_t INTENCLR;                          /**< Interrupt Enable Clear register., offset: 0xC */
  __IO uint32_t TIMEOUT;                           /**< Time-out value register., offset: 0x10 */
  __IO uint32_t CLKDIV;                            /**< Clock pre-divider for the entire I2C interface. This determines what time increments are used for the MSTTIME register, and controls some timing of the Slave function., offset: 0x14 */
  __I  uint32_t INTSTAT;                           /**< Interrupt Status register for Master, Slave, and Monitor functions., offset: 0x18 */
       uint8_t RESERVED_0[4];
  __IO uint32_t MSTCTL;                            /**< Master control register., offset: 0x20 */
  __IO uint32_t MSTTIME;                           /**< Master timing configuration., offset: 0x24 */
  __IO uint32_t MSTDAT;                            /**< Combined Master receiver and transmitter data register., offset: 0x28 */
       uint8_t RESERVED_1[20];
  __IO uint32_t SLVCTL;                            /**< Slave control register., offset: 0x40 */
  __IO uint32_t SLVDAT;                            /**< Combined Slave receiver and transmitter data register., offset: 0x44 */
  __IO uint32_t SLVADR[4];                         /**< Slave address register., array offset: 0x48, array step: 0x4 */
  __IO uint32_t SLVQUAL0;                          /**< Slave Qualification for address 0., offset: 0x58 */
       uint8_t RESERVED_2[36];
  __I  uint32_t MONRXDAT;                          /**< Monitor receiver data register., offset: 0x80 */
} I2C_Type;

/* ----------------------------------------------------------------------------
   -- I2C Register Masks
   ---------------------------------------------------------------------------- */

/*!
 * @addtogroup I2C_Register_Masks I2C Register Masks
 * @{
 */

/*! @name CFG - Configuration for shared functions. */
/*! @{ */
#define I2C_CFG_MSTEN_MASK                       (0x1U)
#define I2C_CFG_MSTEN_SHIFT                      (0U)
/*! MSTEN - Master Enable. When disabled, configurations settings for the Master function are not
 *    changed, but the Master function is internally reset.
 *  0b0..Disabled. The I2C Master function is disabled.
 *  0b1..Enabled. The I2C Master function is enabled.
 */
#define I2C_CFG_MSTEN(x)                         (((uint32_t)(((uint32_t)(x)) << I2C_CFG_MSTEN_SHIFT)) & I2C_CFG_MSTEN_MASK)
#define I2C_CFG_SLVEN_MASK                       (0x2U)
#define I2C_CFG_SLVEN_SHIFT                      (1U)
/*! SLVEN - Slave Enable. When disabled, configurations settings for the Slave function are not
 *    changed, but the Slave function is internally reset.
 *  0b0..Disabled. The I2C slave function is disabled.
 *  0b1..Enabled. The I2C slave function is enabled.
 */
#define I2C_CFG_SLVEN(x)                         (((uint32_t)(((uint32_t)(x)) << I2C_CFG_SLVEN_SHIFT)) & I2C_CFG_SLVEN_MASK)
#define I2C_CFG_MONEN_MASK                       (0x4U)
#define I2C_CFG_MONEN_SHIFT                      (2U)
/*! MONEN - Monitor Enable. When disabled, configurations settings for the Monitor function are not
 *    changed, but the Monitor function is internally reset.
 *  0b0..Disabled. The I2C Monitor function is disabled.
 *  0b1..Enabled. The I2C Monitor function is enabled.
 */
#define I2C_CFG_MONEN(x)                         (((uint32_t)(((uint32_t)(x)) << I2C_CFG_MONEN_SHIFT)) & I2C_CFG_MONEN_MASK)
#define I2C_CFG_TIMEOUTEN_MASK                   (0x8U)
#define I2C_CFG_TIMEOUTEN_SHIFT                  (3U)
/*! TIMEOUTEN - I2C bus Time-out Enable. When disabled, the time-out function is internally reset.
 *  0b0..Disabled. Time-out function is disabled.
 *  0b1..Enabled. Time-out function is enabled. Both types of time-out flags will be generated and will cause
 *       interrupts if they are enabled. Typically, only one time-out will be used in a system.
 */
#define I2C_CFG_TIMEOUTEN(x)                     (((uint32_t)(((uint32_t)(x)) << I2C_CFG_TIMEOUTEN_SHIFT)) & I2C_CFG_TIMEOUTEN_MASK)
#define I2C_CFG_MONCLKSTR_MASK                   (0x10U)
#define I2C_CFG_MONCLKSTR_SHIFT                  (4U)
/*! MONCLKSTR - Monitor function Clock Stretching.
 *  0b0..Disabled. The Monitor function will not perform clock stretching. Software or DMA may not always be able
 *       to read data provided by the Monitor function before it is overwritten. This mode may be used when
 *       non-invasive monitoring is critical.
 *  0b1..Enabled. The Monitor function will perform clock stretching in order to ensure that software or DMA can
 *       read all incoming data supplied by the Monitor function.
 */
#define I2C_CFG_MONCLKSTR(x)                     (((uint32_t)(((uint32_t)(x)) << I2C_CFG_MONCLKSTR_SHIFT)) & I2C_CFG_MONCLKSTR_MASK)
/*! @} */
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
