HappyNapalm/HAD_CLOCK_191211/firmware/Capt_testboard_code/capt_testboard/capt_acomp/drivers/fsl_syscon_connections.h

/*
 * Copyright  2018 NXP
 * All rights reserved.
 *
 *
 * SPDX-License-Identifier: BSD-3-Clause
 */

#ifndef _FSL_SYSCON_CONNECTIONS_
#define _FSL_SYSCON_CONNECTIONS_

#include "fsl_common.h"

/*******************************************************************************
 * Definitions
 ******************************************************************************/
/* Component ID definition, used by tools. */
#ifndef FSL_COMPONENT_ID
#define FSL_COMPONENT_ID "platform.drivers.syscon_connections"
#endif

/*!
 * @addtogroup syscon
 * @{
 */

/*!
 * @name Syscon multiplexing connections
 * @{
 */

/*! @brief Periphinmux IDs */
#define PINTSEL_ID 0x178U
#define SYSCON_SHIFT 20U

/*! @brief SYSCON connections type */
typedef enum _syscon_connection_t
{
    /*!< Pin Interrupt. */
    kSYSCON_GpioPort0Pin0ToPintsel = 0U + (PINTSEL_ID << SYSCON_SHIFT),
    kSYSCON_GpioPort0Pin1ToPintsel = 1U + (PINTSEL_ID << SYSCON_SHIFT),
    kSYSCON_GpioPort0Pin2ToPintsel = 2U + (PINTSEL_ID << SYSCON_SHIFT),
    kSYSCON_GpioPort0Pin3ToPintsel = 3U + (PINTSEL_ID << SYSCON_SHIFT),
    kSYSCON_GpioPort0Pin4ToPintsel = 4U + (PINTSEL_ID << SYSCON_SHIFT),
    kSYSCON_GpioPort0Pin5ToPintsel = 5U + (PINTSEL_ID << SYSCON_SHIFT),

    kSYSCON_GpioPort0Pin7ToPintsel = 7U + (PINTSEL_ID << SYSCON_SHIFT),
    kSYSCON_GpioPort0Pin8ToPintsel = 8U + (PINTSEL_ID << SYSCON_SHIFT),
    kSYSCON_GpioPort0Pin9ToPintsel = 9U + (PINTSEL_ID << SYSCON_SHIFT),
    kSYSCON_GpioPort0Pin10ToPintsel = 10U + (PINTSEL_ID << SYSCON_SHIFT),
    kSYSCON_GpioPort0Pin11ToPintsel = 11U + (PINTSEL_ID << SYSCON_SHIFT),
    kSYSCON_GpioPort0Pin12ToPintsel = 12U + (PINTSEL_ID << SYSCON_SHIFT),
    kSYSCON_GpioPort0Pin13ToPintsel = 13U + (PINTSEL_ID << SYSCON_SHIFT),
    kSYSCON_GpioPort0Pin14ToPintsel = 14U + (PINTSEL_ID << SYSCON_SHIFT),
    kSYSCON_GpioPort0Pin15ToPintsel = 15U + (PINTSEL_ID << SYSCON_SHIFT),
    kSYSCON_GpioPort0Pin16ToPintsel = 16U + (PINTSEL_ID << SYSCON_SHIFT),
    kSYSCON_GpioPort0Pin17ToPintsel = 17U + (PINTSEL_ID << SYSCON_SHIFT),
    kSYSCON_GpioPort0Pin18ToPintsel = 18U + (PINTSEL_ID << SYSCON_SHIFT),
    kSYSCON_GpioPort0Pin19ToPintsel = 19U + (PINTSEL_ID << SYSCON_SHIFT),
    kSYSCON_GpioPort0Pin20ToPintsel = 20U + (PINTSEL_ID << SYSCON_SHIFT),
    kSYSCON_GpioPort0Pin21ToPintsel = 21U + (PINTSEL_ID << SYSCON_SHIFT),
    kSYSCON_GpioPort0Pin22ToPintsel = 22U + (PINTSEL_ID << SYSCON_SHIFT),
    kSYSCON_GpioPort0Pin23ToPintsel = 23U + (PINTSEL_ID << SYSCON_SHIFT),
    kSYSCON_GpioPort0Pin24ToPintsel = 24U + (PINTSEL_ID << SYSCON_SHIFT),
    kSYSCON_GpioPort0Pin25ToPintsel = 25U + (PINTSEL_ID << SYSCON_SHIFT),
    kSYSCON_GpioPort0Pin26ToPintsel = 26U + (PINTSEL_ID << SYSCON_SHIFT),
    kSYSCON_GpioPort0Pin27ToPintsel = 27U + (PINTSEL_ID << SYSCON_SHIFT),
    kSYSCON_GpioPort0Pin28ToPintsel = 28U + (PINTSEL_ID << SYSCON_SHIFT),
    kSYSCON_GpioPort0Pin29ToPintsel = 29U + (PINTSEL_ID << SYSCON_SHIFT),
    kSYSCON_GpioPort0Pin30ToPintsel = 30U + (PINTSEL_ID << SYSCON_SHIFT),
} syscon_connection_t;

/*@}*/

#endif /* _FSL_SYSCON_CONNECTIONS_ */
