HappyNapalm/HAD_CLOCK_191211/firmware/Capt_testboard_code/capt_testboard/led_blinky/source/led_blinky.c

/*
 * Copyright 2017 NXP
 * All rights reserved.
 *
 * SPDX-License-Identifier: BSD-3-Clause
 */

#include "board.h"
#include "fsl_gpio.h"

#include "pin_mux.h"
/*******************************************************************************
 * Definitions
 ******************************************************************************/
#define BOARD_LED_PORT 0U
#define BOARD_LED_PIN 13U

/*******************************************************************************
 * Prototypes
 ******************************************************************************/

/*******************************************************************************
 * Variables
 ******************************************************************************/
volatile uint32_t g_systickCounter;

/*******************************************************************************
 * Code
 ******************************************************************************/
void SysTick_Handler(void)
{
    if (g_systickCounter != 0U)
    {
        g_systickCounter--;
    }
}

void SysTick_DelayTicks(uint32_t n)
{
    g_systickCounter = n;
    while (g_systickCounter != 0U)
    {
    }
}

/*!
 * @brief Main function
 */
int main(void)
{
    /* Define the init structure for the output LED pin*/
    gpio_pin_config_t led_config = {
        kGPIO_DigitalOutput,
        0,
    };

    /* Board pin init */
    BOARD_InitPins();
    BOARD_InitBootClocks();
    BOARD_InitDebugConsole();

    /* Init output LED GPIO. */
    GPIO_PortInit(GPIO, BOARD_LED_PORT);
    GPIO_PinInit(GPIO, BOARD_LED_PORT, BOARD_LED_PIN, &led_config);

    /* Set systick reload value to generate 1ms interrupt */
    if (SysTick_Config(SystemCoreClock / 1000U))
    {
        while (1)
        {
        }
    }

    while (1)
    {
        /* Delay 1000 ms */
        SysTick_DelayTicks(1000U);
        GPIO_PortToggle(GPIO, BOARD_LED_PORT, 1u << BOARD_LED_PIN);
    }
}
